ewinkuo1-sudo/diy-lm3886-amplifier/docs/03-整機配件需求.md

# BOM 與整機配件

> 採購資訊的單一入口是 [00 採購總表](00-採購總表.md)；本頁為其附錄，保留設計需求與原始判斷依據。

最新[露天商品直達連結](11-露天購物連結.md)已另列2026-09-18查價、包裝與待確認條件；以下保留設計需求。

> V0.3／2026-09-16：採用 C 方案，只有變壓器與 LM3886T 已購；額定電流、保護與實際功率待確認。

[電路 BOM](../electrical/bom-draft.csv) 由 KiCad 匯出的 netlist 產生，涵蓋 43 個放大板元件；另有[電源次級 BOM](../electrical/psu-bom-draft.csv) 的 15 個元件。`footprint` 留空代表尚未核對實際尺寸，不能據此直接下單 PCB。沒有價格欄：本次未查供應商即時庫存與報價。

## 放大板選材

- IC：LM3886T ×2 為設計用量；已訂拆機品，訂單數量與 /NOPB 待核對；封裝與引腳彎折須依實際訂購型號核對。
- 小訊號電阻：1% 金屬膜，除 BOM 另列者外以 0.25W 起選。
- Zobel 與輸出阻尼電阻：低電感、至少 2W，保留散熱空間，量測高頻下溫升。
- 0.7µH 電感：空心，初選 DCR ≤0.05Ω，線徑與安裝須能承受至少 4A 峰值及測試溫升；40W／8Ω 的需求為 3.16A 峰值。此項仍需料號或繞製規格。
- 2.2µF 輸入電容：薄膜、≥63V。
- 47µF 回授電容：真正無極性／雙極性、≥63V；不把一般電解正反接的問題留到焊接時猜測。
- 電源／靜音電解：≥63V，依原理圖正負極組裝。100nF 去耦可用 X7R 或薄膜；Zobel 用薄膜。

## 尚未畫入放大板的整機需求

| 部件 | 數量 | 初選條件／待辦 |
|---|---:|---|
| 內建環形變壓器 | 1 | 已訂 AC110V、兩組獨立 22Vac＋單 12Vac；賣場 200W 不作已確認 VA，電流／頻率／調整率待核對 |
| 整流與大電容 | 1 組 | 電源次級 BOM 已列兩橋、4×10,000µF／63V、洩放及旁路；料號與散熱待選 |
| AC 入口／一次側保險絲／開關 | 1 組 | 核對一次側料件後決定電流額定與分斷能力 |
| 浪湧控制與旁路 | 1 組 | 含快速關開及失效情境，待設計 |
| 隔離輔助電源／輔助繞組 | 1 組 | 供保護繼電器與啟停控制，待決定電壓及容量 |
| 電源動態能力／儲能 | 1 組 | 2×40W 試算同相正弦時，每軌訊號峰值約 6.32A，另有靜態電流；由實際電源與電容共同承擔，待選型後驗證 |
| 散熱器 | 2 | 每聲道 ≤0.4°C/W，按實際機內氣流及安裝方向核對 |
| 絕緣導熱介面及螺絲套 | 2 組 | 確認熱阻 ≤0.3°C/W 與電氣絕緣；不只核對厚度 |
| 絕緣 RCA 插座 | 2 | 機殼接地規劃完成前不靠插座形成多點地 |
| 喇叭接線柱 | 4 | 額定電流、絕緣距離與面板固定待選；原型先接假負載 |
| 機殼／固定件 | 1 組 | 依散熱器、電源界面及 PCB 實際尺寸設計；尚無加工圖 |
| 電源輸入保護 | 1 組 | 下一版加入適合雙軌電源的保護；不得直接套用未定案的保險絲額定 |
| 喇叭 DC 保護／繼電器 | 1 組 | 下一版設計，包含輔助電源及 DC 斷開能力驗證 |
| 非感性假負載 | 2 | 8Ω、連續至少 100W，按額定安裝散熱 |

內建電源的架構與次級整流草案已完成；一次側接線、軟啟動及保護控制尚未完成。整機 BOM 尚須加入機殼 PE 接點、屏障、端子與線束。參見[內建電源規劃](05-內建電源與機構.md)。
