ewinkuo1-sudo/diy-lm3886-amplifier/docs/09-採購後修訂計畫.md

# 採購後修訂計畫（2026-09-16）

> 採購資訊的單一入口是 [00 採購總表](00-採購總表.md)；本頁為其附錄，保留設計需求與原始判斷依據。

**2026-09-18 選料更新：**已登記使用者預計下單清單；47µF／470µF 各保留兩款候選，尚未決定。全部未購，詳見 [目前候選與封裝影響](10-預計下單清單.md)。既有 PCB／3D 外框尚未依此換料。

本文件取代 V0.2 的變壓器採購候選與功率驗收目標。使用者確認兩個商品均已下單、正在等到貨；沒有到貨量測。

## 使用者選定 C 方案：完整雙聲道

- 兩聲道各一顆 LM3886T，共用正負主電源；雙橋指正、負電源整流架構，不代表左右聲道各有獨立電源。
- 主整流橋 2 顆、10,000µF／63V 主濾波電容 4 顆（每軌 2 顆並聯）全部待購；容量配置已選，實際品牌／系列、紋波額定及尺寸待選。
- 整機納入散熱與絕緣、雙聲道喇叭 DC 保護、開機延遲／掉電斷開、浪湧限制、保險絲、機殼 PE 接地及端子配線。這些均未購且尚未完成細部設計。
- 優先評估 12Vac 輔助繞組供保護與控制，模組供電類型及繞組電流確認後選型。
- 四顆主電容不代表輸出瓦數增加；功率仍受變壓器、供電下陷與散熱限制。單聲道先測只是驗證順序，最終交付目標是完整雙聲道。

## 已下單與設計方向

- [蝦皮環形變壓器](https://shopee.tw/product/1151719/361359378)：賣場標示 200W、輸入 AC110V、輸出 (0–22)/(0–22)＋(0–12)，兩組主次級可串聯；直徑 120mm、高 43mm、約 2.4kg。這些是 2026-09-16 查閱的商品宣稱，不是驗收數據。連續 VA、各繞組電流、頻率額定、調整率、熱保護及線色相位待確認；不得直接把 200W 當 200VA 或推定每繞組電流。
- [露天 LM3886T](https://www.ruten.com.tw/item/22405749782156/)：標題為二手原裝拆機，物品狀況欄卻寫全新，來源與健康狀態待核對。已確認此連結下單，訂單數量待確認；設計需 2 顆，舊紀錄 4 顆不作已確認數量。不能把賣場 T 型號直接登記為已確認 /NOPB。
- 維持兩聲道各一顆 LM3886T、非橋接非並聯、8Ω、Z10 RCA 控制音量；放大板元件值暫不更動。
- 取消另購原 300VA／2×25Vac 候選。先沿用兩組獨立次級各接全橋、橋輸出串聯形成正負軌的架構；此接法下 AC 次級不得另行串接。到貨需先核對繞組獨立性與標記。
- 依 C 方案選定每軌 20,000µF、63V 主電容配置，實際料號待選；保留原散熱初選，不因電壓降低而逕行縮小散熱器。保險絲、浪湧限制與整流橋需依實際額定再選。

## 電壓與功率：估算而非額定

雙橋每軌有兩顆導通二極體。若次級確實為 22Vrms、每顆壓降取 1.1V，濾波峰值約 22×√2−2.2 = 28.9V，尚未扣紋波與負載下陷。因此「約 ±30V 等級」不代表固定供電。

沿用舊版的 +10% 市電、+8% 空載調整率、每顆二極體 0.6V 假設，得到 22×1.10×1.08×√2−1.2 ≈ 35.8V／軌。調整率未知，這只是情境計算，不能作最大電壓保證。

先以每聲道約 30～40W／8Ω 為探索範圍；不再要求必達 2×40W，也不沿用 50W 延伸驗收。先量削波點與溫升，再決定可標示的雙聲道連續功率。TI 的 ±28V、8Ω、典型 38W 是元件參考條件，並非本機保證。[TI LM3886](https://www.ti.com/product/LM3886)

## 12Vac 輔助繞組

優先供喇叭保護與啟停控制，但待確認繞組電流及模組 AC／DC 輸入要求。12Vac 經全橋濾波約為 15～16Vdc，空載可能更高；若模組要求 DC12V，需適當穩壓。暫緩另購輔助變壓器與未定型保護板。

## 到貨與下一步

1. 核對變壓器標籤、繞組線色／相位、額定電流、尺寸及配件；取得賣家資料後更新電源模型。機殼與保險絲待此步再選。
2. 核對 IC 實收數量、完整打標及批號；外觀不能證明真偽。T 背板為負電源，保留絕緣導熱介面與螺絲絕緣套。
3. 每顆先裝散熱器，用限流雙電源檢查靜態電流、輸出直流、波形與溫升；先單聲道、假負載測試。
4. 電源獨立量測空載、負載、紋波及放電，再整合雙聲道；DC 保護與啟停驗證後才接喇叭。
5. 放大板小零件可沿用候選清單；PCB、機殼、保護板與一次側元件仍未定案。

## 圖面與 PDF 版本

V0.3 已更新兩份 KiCad 圖的供電與版本標示、PDF／PNG 預覽、BOM 及 22Vac 電源／熱估算。原放大電路與雙橋四電容網路保留；12Vac 控制與一次側只列功能框架，待詳細設計。驗證結果見 electrical/validation.md，沒有硬體量測。

新版 PDF 位於 output/pdf/，包含現行設計彙整及採購勾選清單。2026-09-11 舊 PDF 僅作歷史快照，不作現行採購依據。六張導讀圖已於 2026-09-17 同步方案 C V0.3，見 [導讀圖索引](diagrams/README.md)；舊圖由 Git 歷史保留。
