ewinkuo1-sudo/diy-lm3886-amplifier/docs/10-預計下單清單.md

# 預計下單零件與替代候選（2026-09-18）

> 採購資訊的單一入口是 [00 採購總表](00-採購總表.md)；本頁為其附錄，保留設計需求與原始判斷依據。

使用者提供文字清單與購物車截圖，並確認 **47µF 與 470µF 的兩組品牌都先保留候選，尚未決定**。以下全部是預計下單／候選，不是已購、已出貨或到料紀錄；沒有代為購買。

[露天購買連結、下標選項及其餘待買候選](11-露天購物連結.md)已補齊；NCC店未滿$100不出貨等限制見該頁。

## 文字清單：佑昇音響／真合貿易有限公司

規格、金額及出貨天數原依使用者貼文記錄；2026-09-18已補上商品直達連結並核對商品頁，未結帳。價格暫按每顆新台幣計算；14／21 天為賣場出貨描述，不是到貨承諾。

| 品牌／系列／料號 | 規格 | 數量 | 對應原理圖 | 顯示價格／顆 | 出貨描述 | 狀態 |
|---|---|---:|---|---:|---|---|
| [Vishay BCcomponents PR02](https://www.ruten.com.tw/item/21452091096054/) | 2.2kΩ / 2W / 1% | 2 | R201, R202 | $20 | 21天內 | 預計下單，未購 |
| [RNU2（製造商待確認）](https://www.ruten.com.tw/item/21308069698811/) | 2.7Ω / 2W | 2 | R5, R105 | $5 | 21天內 | 預計下單，未購 |
| [Vishay BCcomponents PR02](https://www.ruten.com.tw/item/21452091095918/) | 10Ω / 2W / 1% | 2 | R7, R107 | $20 | 21天內 | 預計下單，未購 |
| [Vishay BCcomponents MRS25](https://www.ruten.com.tw/item/21505371267166/) | 1kΩ / 0.6W / 1% | 4 | R3, R103, R6, R106 | $5 | 14天內 | 預計下單，未購 |
| [Vishay BCcomponents MRS25](https://www.ruten.com.tw/item/21505371700382/) | 20kΩ / 0.6W / 1% | 2 | R4, R104 | $5 | 21天內 | 預計下單，未購 |
| [Vishay BCcomponents MRS25](https://www.ruten.com.tw/item/21505371269809/) | 22kΩ / 0.6W / 1% | 4 | R2, R102, R8, R108 | $5 | 21天內 | 預計下單，未購 |
| [Vishay BCcomponents MRS25](https://www.ruten.com.tw/item/21505371254476/) | 1MΩ / 0.6W / 1% | 2 | R1, R101 | $5 | 21天內 | 預計下單，未購 |
| [CDE 361R / 361R101M100EG2](https://www.ruten.com.tw/item/22111174641617/) | 100µF / 100V | 2 | C8, C108 | $48 | 21天內 | 預計下單，未購 |
| [ROE EKE](https://www.ruten.com.tw/item/21513740997288/) | 470µF / 63V | 4 | C6, C7, C106, C107 | $90 | 21天內 | 候選，二擇一 |
| [ROE EGW](https://www.ruten.com.tw/item/21515914332545/) | 47µF / 63V / 23Vac / BP-NP | 2 | C2, C102 | $300 | 21天內 | 候選，二擇一 |
| [WIMA MKS4](https://www.ruten.com.tw/item/21304180923597/) | 2.2µF / 100V / 5% | 2 | C1, C101 | $70 | 14天內 | 預計下單，未購 |
| [WIMA MKS2 / MKS2D031001A00JSSD](https://www.ruten.com.tw/item/21304114150484/) | 100nF / 100V / 5mm | 8 | C3, C4, C5, C103, C104, C105, C205, C206 | $19 | 14天內 | 預計下單，未購 |
| [CDE 381LX / 381LX103M063A052](https://www.ruten.com.tw/item/22102647676193/) | 10000µF / 63V | 4 | C201, C202, C203, C204 | $185 | 14天內 | 預計下單，未購 |
## 截圖中的替代候選

| 用途 | 文字清單 | 截圖候選 | 實際需求 |
|---|---|---|---|
| C2／C102 回授無極性電容 | ROE EGW 47µF／63V，$300×2 | [Mundorf E-Cap RAW 47µF／100V](https://www.ruten.com.tw/item/21724493448626/)，$190×2；管迷；標示3天內出貨 | 合計只需2顆，兩款尚未決定 |
| C6／C7／C106／C107 本地儲能 | ROE EKE 470µF／63V，$90×4 | [NCC KY 470µF／63V](https://www.ruten.com.tw/item/22339798786419/)，$15×4；f88911；標示3天內出貨、16×20 mm | 合計只需4顆，兩款尚未決定 |

截圖運費：管迷郵寄 $50、f88911 黑貓 $30，均為畫面當時顯示，未確認結帳。Mundorf 商品標題的「47µf」按 47µF 登記。截圖不是訂單證明。

## 數量與金額核對

文字清單共有13列、40顆，對應40個不同的原理圖位置；加入替代候選後仍為40個需求位置，不是46顆必買。所有電阻數量相符；100nF ×8 正好涵蓋兩聲道去耦4顆、Zobel 2顆、電源板旁路2顆。

若貼文價格均為單價，以下為**零件小計，不含運費與折扣**：

| 47µF 選擇 | 470µF 選擇 | 試算小計 |
|---|---|---:|
| ROE EGW | ROE EKE | $2238 |
| ROE EGW | 日本化工 NCC KY（賣場標示） | $1938 |
| Mundorf E-Cap RAW | ROE EKE | $2018 |
| Mundorf E-Cap RAW | 日本化工 NCC KY（賣場標示） | $1718 |

## 對目前 PCB／3D 的影響

這次更新選料紀錄，**未把商品名稱直接視為已驗證封裝，也未重畫 PCB**。既有 A＋B＋C 圖集是選料前的 V0.3 快照；圖中的高度及外框仍為假設。

- **C2／C102：必須重新安排臥式封裝。** ROE 文字清單與 Mundorf 截圖均為臥式候選，不能直接沿用目前立式 `BP_D10_P5` 的孔位／外框。需先確認本體長度、直徑、引腳彎折與安裝腳距。
- **470µF：NCC 候選的賣場尺寸與現板不同。** 截圖標示16×20 mm，現有占位為 Ø12.5 mm／腳距5 mm；若採 NCC，需核對完整料號與腳距並調整外框、間距及模型。ROE EKE 也未取得實體尺寸。
- **100µF：CDE 已提供完整料號。** 100V 為較高標示耐壓，仍需核對容量容差、尺寸、漏電等條件，不表示能直接塞進原 Ø8 占位。
- **主電容：CDE 381LX 已提供完整料號，但為牛角型。** 不只查腳距，也要確認接腳形狀、鑽孔及本體尺寸；現有1.3 mm孔不視為已合格。
- **電阻：軸向腳距需按本體與彎腳確認。** PR02、MRS25 的完整訂購碼尚未提供；RNU2 的4.5×15 mm只記為賣場描述，低電感特性仍待資料核對。
- **WIMA：15 mm／5 mm 腳距與目前占位方向一致，但本體寬高與完整型號仍需逐項核對。** MKS2 的完整料號已記錄；MKS4 尚缺完整訂購碼。

下一次修改封裝時，以本表候選＋原廠尺寸圖／實物為依據；再同步原板、3D、裝配圖與 DRC。這次沒有新增 ERC／DRC 或硬體測試。

## 尚未包含的零件

整流橋、次級保險絲及座、0.7µH電感、板端接頭／跳線、RCA與喇叭端子、散熱器與絕緣件、機殼固定件、保護／啟停／輔助電源及一次側配件仍需確認。變壓器與LM3886T沿用既有已訂待到貨紀錄。

## 資料來源與狀態

本表來源僅為使用者2026-09-18提供的文字與截圖，不把商品標題當成原廠認證。完整結構化紀錄見 [JSON](10-planned-parts.json)；已購狀態見 [採購紀錄](08-採購狀態.md)。未把含商店與價格的原始截圖上傳到專案。
