ewinkuo1-sudo/diy-lm3886-amplifier/docs/11-露天購物連結.md

# 露天商品連結與待買候選（2026-09-18）

> 採購資訊的單一入口是 [00 採購總表](00-採購總表.md)；本頁為其附錄，保留設計需求與原始判斷依據。

這份清單可直接點到商品頁，再由使用者選規格、數量與加入購物車。**沒有新增訂單或代加購物車；47µF、470µF仍各自二擇一、尚未決定。** 全部商品頁已於2026-09-18開啟核對，看到購物操作入口；價格、庫存、可選規格與出貨條件以結帳當時為準。

「原清單相符」只代表賣場描述符合使用者選的候選，並非原廠資料、真偽、實測或PCB封裝核對。「待確認／暫緩」的新增候選，應先解決該列缺項才購買。這不是一鍵全買清單。

## 原本15項候選的商品直達連結

前13項為佑昇音響／真合貿易有限公司（yosontw），最後兩項為截圖指定賣家。數量為雙聲道設計需求，價格為單顆；完整位置對照與原始採購紀錄見[原清單](10-預計下單清單.md)。

| 商品直達頁 | 規格 | 設計需求 | 單顆參考價 | 選項／注意 |
|---|---|---:|---:|---|
| [Vishay BCcomponents PR02](https://www.ruten.com.tw/item/21452091096054/) | 2.2kΩ / 2W / 1% | 2 | $20 | 單件商品；需求2顆 |
| [RNU2（製造商待確認）](https://www.ruten.com.tw/item/21308069698811/) | 2.7Ω / 2W | 2 | $5 | 單件商品；需求2顆 |
| [Vishay BCcomponents PR02](https://www.ruten.com.tw/item/21452091095918/) | 10Ω / 2W / 1% | 2 | $20 | 單件商品；需求2顆 |
| [Vishay BCcomponents MRS25](https://www.ruten.com.tw/item/21505371267166/) | 1kΩ / 0.6W / 1% | 4 | $5 | 單件商品；需求4顆 |
| [Vishay BCcomponents MRS25](https://www.ruten.com.tw/item/21505371700382/) | 20kΩ / 0.6W / 1% | 2 | $5 | 單件商品；需求2顆 |
| [Vishay BCcomponents MRS25](https://www.ruten.com.tw/item/21505371269809/) | 22kΩ / 0.6W / 1% | 4 | $5 | 單件商品；需求4顆 |
| [Vishay BCcomponents MRS25](https://www.ruten.com.tw/item/21505371254476/) | 1MΩ / 0.6W / 1% | 2 | $5 | 單件商品；需求2顆 |
| [CDE 361R](https://www.ruten.com.tw/item/22111174641617/) | 100µF / 100V | 2 | $48 | 選「1個」，數量2 |
| [ROE EKE](https://www.ruten.com.tw/item/21513740997288/) | 470µF / 63V | 4 | $90 | 單件商品；需求4顆；與同組另一款二擇一 |
| [ROE EGW](https://www.ruten.com.tw/item/21515914332545/) | 47µF / 63V / 23Vac / BP-NP | 2 | $300 | 單件商品；需求2顆；與同組另一款二擇一 |
| [WIMA MKS4](https://www.ruten.com.tw/item/21304180923597/) | 2.2µF / 100V / 5% | 2 | $70 | 選「1顆」，數量2；不要選10顆包裝 |
| [WIMA MKS2](https://www.ruten.com.tw/item/21304114150484/) | 100nF / 100V / 5mm | 8 | $19 | 選「1個」，數量8 |
| [CDE 381LX](https://www.ruten.com.tw/item/22102647676193/) | 10000µF / 63V | 4 | $185 | 選「1個」，數量4；不要選10個包裝 |
| [Mundorf E-Cap RAW](https://www.ruten.com.tw/item/21724493448626/) | 47µF / 100V / 無極性 | 2 | $190 | 單件商品；需求2顆；與同組另一款二擇一 |
| [日本化工 NCC KY（賣場標示）](https://www.ruten.com.tw/item/22339798786419/) | 470µF / 63V | 4 | $15 | 單件商品；需求4顆；與同組另一款二擇一 |

- **NCC賣場最低出貨金額：**[f88911公告](https://www.ruten.com.tw/store/f88911/)表示未含運低於$100不出貨；4顆×$15＝$60尚未達門檻。購買前確認合單或出貨條件，勿把多買的備品當成電路需求。
- WIMA MKS4頁面含1顆／10顆選項；CDE 381LX含1個／10個。表內以單件需求計，不能按最低顯示價誤選整包數量。
- Mundorf賣方新增尺寸描述為本體Ø14×37mm、引線長60mm，仍需原廠／到料核對；不把引線長當PCB腳距。NCC原款是16×20mm，不是同店的12.5×30mm款。
- 原13項小計仍為$2238；依兩組替代選擇為$1938／$2018／$1718，皆未含運、最低出貨門檻及新增配件。

## 尚未選購的板上元件與整機配件

以下都是新找到的候選來源，**沒有替使用者定案**。需求涵蓋現有三板及整機配件；額外保護模組尚未整合原理圖。包裝單位不明的條目已標出，不能把「設計需求」直接當下標件數。

### 電源板

| 商品直達頁 | 設計需求 | 選項／頁面價格 | 選型狀態與待核對 |
|---|---|---|---|
| [KBPC2510 整流橋](https://www.ruten.com.tw/item/22605098060064/) | 2個／BR1、BR2 | 標題25A／1000V，單位數量先確認；$51 | 待確認：完整廠牌、KBPC／KBPC-W端子形態、腳位、外形與散熱；25A不能當作本板持續輸出能力。 |
| [5×20mm 保險絲座](https://www.ruten.com.tw/item/21840721329469/) | 2個／F201、F202 | 保險絲座，不把附帶保險絲當已選定；$4 | 待確認：PCB安裝型態、腳距、孔徑、DC電壓／電流額定；5×20是保險管尺寸，不是焊腳距。 |

### 放大板

| 商品直達頁 | 設計需求 | 選項／頁面價格 | 選型狀態與待核對 |
|---|---|---|---|
| [0.7µH 空心電感](https://www.ruten.com.tw/item/22615433056210/) | 2個／L1、L2 | 每件1只，需求2；$379 | 待確認：賣方稱線徑2.1mm、外徑13.5mm、長10.5mm、腳距28mm；DCR≤0.05Ω、≥4A峰值與公差未證實，2.1mm線徑須重新核對PCB孔徑。 |

### 接插件

| 商品直達頁 | 設計需求 | 選項／頁面價格 | 選型狀態與待核對 |
|---|---|---|---|
| [KF301 2P／5.08mm](https://www.ruten.com.tw/item/22409916143944/) | 6個 | 2P，賣方標300V／16A、14–22AWG；確認1件所含數量；$1 | 待確認：J1／J2各2個＋J201／J202各1個；廠牌、孔徑、插線方向與載流條件，不能只憑同為KF301認定相容。 |
| [KF301 3P／5.08mm](https://www.ruten.com.tw/item/22410924930141/) | 3個 | 3P，賣方標300V／16A、14–22AWG；確認1件所含數量；$2 | 待確認：左右板J5各1個＋J203一個；核對VCC/GND/VEE順序、孔徑、插線方向與載流。 |
| [2.54mm 單排針 1×40P](https://www.ruten.com.tw/item/21839712907740/) | 2段×2pin | 一條40pin可裁出兩段；先確認單件包裝；$3 | 待確認：RUN JP1／JP2，與跳線帽配合高度、≥60VDC絕緣額定；不是排母。 |
| [2.54mm 跳線帽](https://www.ruten.com.tw/item/22410924645672/) | 2個 | 商品為100只包裝；買1包會剩98只；$23／100只 | 待確認：≥60VDC絕緣額定；僅採購包裝超額，不增加設計需求。 |

### 機殼接插件

| 商品直達頁 | 設計需求 | 選項／頁面價格 | 選型狀態與待核對 |
|---|---|---|---|
| [RCA 面板母座](https://www.ruten.com.tw/item/21840724685995/) | 2個 | 紅色1、黑色1；$12 | 待確認：必須附能隔離外殼與金屬面板的完整絕緣墊圈／套管；目前只確認紅黑款商品頁，沒有證明面板絕緣。 |
| [喇叭接線柱](https://www.ruten.com.tw/item/22410923188279/) | 4個 | 標題1只價；需求紅2、黑2，頁面未提供顏色選項，需先確認配色方式；$17 | 待確認：≥60VDC、載流、面板絕緣、開孔及板厚；不是4個單聲道端子組。 |

### 散熱／機構

| 商品直達頁 | 設計需求 | 選項／頁面價格 | 選型狀態與待核對 |
|---|---|---|---|
| [大 TO-3P 雲母絕緣片 22×30mm](https://www.ruten.com.tw/item/22410921549515/) | 2片 | 10張包裝，1包；$23／10張 | 待確認：此為尺寸候選，尚未證明適合LM3886T孔位／金屬背板；整套介面熱阻≤0.3°C/W、耐壓及安裝公差待核對。 |
| [LM3886 用絕緣螺絲套](https://www.ruten.com.tw/item/21711492321878/) | 2個 | 10顆包裝，1包；$20／10顆 | 待確認：賣方列外徑6mm／內徑3mm；套肩長、IC孔位與實際螺絲配合；螺絲套不取代導熱絕緣片。 |
| [TS-KS101 導熱膏](https://www.ruten.com.tw/item/22410921235113/) | 裝配適量 | 45g包裝，需求1份；$57 | 待確認：材料導電性與介面相容；導熱膏不能單獨提供LM3886T背板絕緣。 |
| [大型鋁型材散熱器](https://www.ruten.com.tw/item/22407792090091/) | 每聲道1個，條件成立才採買 | 頁面有「200長（批量）」與「100長（批量）」；尺寸與最小包裝需詢明；$1,012–2,531 | 暫緩：標題400×50×200mm，沒有≤0.4°C/W資料，並可能超出機殼空間；僅作詢問熱阻／裁切的來源，未認定合用。若用附散熱器機殼不要重複買。 |
| [430寬全鋁後級機箱](https://www.ruten.com.tw/item/22547543033963/) | 1個 | 有300深度／400深度；以400深度作排布候選，未定案；$3,895–4,285 | 暫緩：賣方400深款內部約330×112×400mm，附兩側散熱器及帶保險電源座；尺寸標題／內文有差異，須取加工圖。散熱片重量不是熱阻，三板／變壓器／保護板仍需排布。 |
| [M3 銅柱、螺絲、螺帽](https://www.ruten.com.tw/item/22601863290504/) | 三片PCB共12支柱，螺絲依安裝方式 | 先選M3，長度待機構定案；銅柱10個/包，若買兩包則20支；螺絲為另一選項；$25–95 | 待確認：板底焊腳間隙、銅柱高度、螺絲長度與接地用途；勿將M4或單買螺母選項當成完整固定組。 |

### 市電／控制

| 商品直達頁 | 設計需求 | 選項／頁面價格 | 選型狀態與待核對 |
|---|---|---|---|
| [AC-01 電源入口＋帶燈開關＋保險座](https://www.ruten.com.tw/item/22410919510431/) | 1組（機殼若已附合用款則免重買） | 賣方標15A／250V，需確認110Vac燈與接口規格；$29 | 暫緩：核對原廠安規、極數、接地端、一次側開關接法、面板尺寸與保險管；保險絲電流尚未決定。 |
| [5×20 延時保險絲系列](https://www.ruten.com.tw/item/22410976060232/) | 至少一次側1＋次級2，最終依保護設計 | 標題1／1.5／2／3／3.15A；沒有可直接指定的正確電流，包裝數量也待確認；$136（單位未明） | 暫緩：變壓器額定電流、浪湧、保護協調、AC/DC分斷能力未定；不保證此系列任一款符合，禁止照頁面預設值購買。 |
| [AC105–235V 軟啟動板](https://www.ruten.com.tw/item/22546454641812/) | 1組 | 接線端子式／插線端子式兩款；接線端子式先列候選；$660 | 暫緩：僅標題電壓範圍涵蓋110V；需電路／額定功率、限流電阻、繼電器、重啟及失效行為，尚未整合設計。 |
| [UPC1237 雙聲道喇叭保護板](https://www.ruten.com.tw/item/22631277223445/) | 1組 | 賣方稱獨立AC12–18V、約3秒延遲、約1VDC起控；$258 | 暫緩：賣家公告部分二手以全新欄位上架，需確認本件狀況。需完整電路、±DC偵測、掉電釋放、繼電器DC分斷能力及12Vac繞組容量；不可將300Wx2文案當規格。 |

### 線束

| 商品直達頁 | 設計需求 | 選項／頁面價格 | 選型狀態與待核對 |
|---|---|---|---|
| [16AWG 黑色矽膠線](https://www.ruten.com.tw/item/22407795970619/) | 長度待機殼排布 | 1米單位；先列候選，不先固定米數；$35／米 | 待確認：銅截面、溫度／電壓額定、端子適配；供次級／DC／喇叭線路評估，不自動作市電或PE線。 |
| [16AWG 紅色矽膠線](https://www.ruten.com.tw/item/22407795970226/) | 長度待機殼排布 | 1米單位；不同電源軌需另做清楚標識；$35／米 | 待確認：同黑色線要求，實際束線載流與溫升仍需驗證。 |
| [20cm 屏蔽訊號線](https://www.ruten.com.tw/item/22325050050240/) | 左右聲道各1段，長度待確認 | 原商品帶XH2.54 3P插頭；$8 | 待確認：現板J1是2P／5.08，不可直接插接，僅線材候選；需改端接、確認屏蔽芯線及實際長度。 |

### 測試

| 商品直達頁 | 設計需求 | 選項／頁面價格 | 選型狀態與待核對 |
|---|---|---|---|
| [8Ω／100W 鋁殼電阻](https://www.ruten.com.tw/item/21840720484921/) | 2個 | 標稱8Ω／100W；散熱器另需核算；$40 | 未符合完整需求：賣方未證實非感性及100W額定散熱條件；本頁僅阻值／功率候選，不列為已核准假負載，不可據此做高頻驗收。 |

## 尚未補到可採用商品的缺項

不是所有缺項都有足夠資料完成選型；以下保留明確缺口，不以規格不符的商品充數。

| 缺項 | 目前限制 |
|---|---|
| 台灣三腳插頭至IEC C13電源線 | 本次尚未取得可核對BSMI與正確接頭的商品直達頁；不要用兩芯線或梅花尾替代。 |
| PE黃綠接地線、環形端子、星形華司與獨立機殼接地螺栓 | 本次未核實適合的完整組合；線徑、端子孔徑、壓接及固定須隨一次側／機構定案。防靜電手環線不能作PE。 |
| 絕緣屏障、套管、護線圈、束線固定與機腳 | 依機殼孔位、線徑及材料等級選定，尚無確定尺寸，未隨意填商品。 |
| 獨立狀態指示燈／輔助穩壓 | 保護板帶LED、AC入口帶燈；先確認是否仍需要獨立前面板燈。12Vac繞組優先，不另訂變壓器或固定DC模組。 |

## 對目前PCB的影響

商品連結不會使PCB自動適配。尤其臥式47µF、Ø16mm NCC、本次0.7µH電感的粗引腳、KBPC端子以及保險絲座都要先取得尺寸，再修改封裝與檢查。此次未修改原理圖、PCB、3D、Gerber或既有PDF，也沒有新增ERC／DRC或硬體測試。

本頁38個商品直達連結包含原候選15項＋新增23項。機器可讀資料：原候選在[10-planned-parts.json](10-planned-parts.json)，新增候選／未解決項目在[11-ruten-shopping-links.json](11-ruten-shopping-links.json)。後續確認選料時，先更新候選狀態，再改PCB，不從本頁反推已購或已驗證。
