ewinkuo1-sudo/diy-lm3886-amplifier/docs/12-機殼候選.md

# 12 機殼候選（淘寶，2026-09-18 查）

> 採購資訊的單一入口是 [00 採購總表](00-採購總表.md)；本頁為其附錄，保留設計需求與原始判斷依據。

**本文件是選型調查，不是採購決定。所有尺寸為賣場標題標示的外部尺寸，未向賣家確認內部可用空間，未核對散熱熱阻，未下單。** 台幣為淘寶頁面自帶換算，**不含運費與集運**。

## 1. 需求推導

依 V0.3 C 方案現有文件：

| 項目 | 尺寸／需求 | 來源 |
|---|---|---|
| 環形變壓器 | Ø120 × H43 mm、約 2.4kg | [09 採購後修訂計畫](09-採購後修訂計畫.md)，賣場宣稱 |
| 電源板 | 160 × 120 mm | [README](../README.md) PCB V0.3 |
| 放大板 | 100 × 90 mm × 2 片 | 同上 |
| 主濾波電容 | 10,000µF／63V × 4，**料號未選** | [08 採購狀態](08-採購狀態.md) |
| 散熱 | 每聲道 ≤0.4 °C/W、介面 ≤0.3 °C/W，每聲道耗散約 20–23W | [05 內建電源與機構規劃](05-內建電源與機構.md)、[02 功率與散熱估算](02-功率與散熱估算.md) |
| 絕緣 | **LM3886T 背板為 VEE**，鎖上接地機殼必須用絕緣介面與螺絲絕緣套 | [01 設計規格](01-設計規格.md) |

推得最低內部空間：

- **寬 ≥ 300 mm** — 環牛（含固定盤約 140）＋電源板 160 並排
- **深 ≥ 250 mm** — 環牛 120 ＋電源板 120／160 前後排列，另需線束空間
- **高 ≥ 90 mm** — 被主電容卡住：Ø35 × 50 mm snap-in 加腳座約需 70 mm；若選牛角式（如 CDE 381LX）需 110 mm 以上

**高度需求會隨主電容選型改變。電容料號未定前，機殼高度不應定案。**

另需容納：市電入口／開關／保險絲、浪湧限制、喇叭 DC 保護板、PE 機殼接地點。

## 2. 首選

### ¥408（約 NT$1,960）4312A 兩側散熱全鋁功放機箱 430 × 120 × 311 mm

<https://www.taobao.com/list/item/V0lLOFBGSFJKTXZKS0Nrc0txaW9FQT09.htm>

唯一三圍全部標示、且兩側帶散熱的候選。430 寬容得下環牛與電源板並排，311 深可容環牛（120）＋電源板（160）前後排列，120 高即使改用牛角電容也有餘裕。評分 5.0。

## 3. 次選

### ¥315（約 NT$1,513）全銀色兩側散熱全鋁機箱 360 × 120 × 275 mm

<https://www.taobao.com/list/item/aG5UZU02OTVHVmZRTGx4TTF5anJRZz09.htm>

比首選便宜約 NT$450，仍在需求之上。深 275 放環牛加電源板較擠，走線與一次側元件空間變少。評分 5.0。

### ¥338（約 NT$1,623）3212 兩側散熱小甲機箱

<https://www.taobao.com/list/item/V3J3K3Fud2RZK1Z3TWJkTzQrMDF2dz09.htm>

型號推測為 320 寬 × 120 高，**深度未標示，需向賣家確認**。評分 5.0。

## 4. 替代路線：素機箱 ＋ 另購散熱鋁擠

總價可壓到約 ¥270（NT$1,300）以下，但**需自行加工開孔、對位，並處理散熱片與機箱的機械與熱介面**。

素機箱：

- ¥198（NT$951）3690 全鋁 360 × 90 — <https://www.taobao.com/list/item/dXJmQnllY3NvNVpSY2h6QU1iblZjdz09.htm>
- ¥178（NT$855）3290 全鋁 320 × 92 — <https://www.taobao.com/list/item/T3N6WjAvQjNBbGcvT0RkR3ZNMDFydz09.htm>

散熱鋁擠：

- ¥59（NT$283）寬 300 × 高 85 mm — <https://www.taobao.com/list/item/WEZZV29JZnRSWTVQRGxQNmlvRHNxZz09.htm>
- ¥75（NT$360）寬 350 × 高 80 mm 高倍齒 — <https://www.taobao.com/list/item/M1RITFJBWWQ2WlBMVHJhZmkwVkpvZz09.htm>
- ¥105（NT$504）寬 300／400 × 高 50 mm — <https://www.taobao.com/list/item/KzlOOUJuaGEvWGVrZHRwc3RuWFBFUT09.htm>

## 5. 已排除

| 商品 | 價格 | 排除理由 |
|---|---|---|
| [1560 機箱 151 × 60，標題寫「適合安裝 LM3886/LM1875」](https://www.taobao.com/list/item/elpFWWwrLzdLejVLczFZNncvZXE3UT09.htm) | ¥85 | **標題有 LM3886 但尺寸不可能**。環牛直徑就 120 mm |
| [BRZHiFi BZ3207S 單側散熱](https://www.taobao.com/list/item/TUtXRjhBN3dENy9jU1E1VkVpZmprdz09.htm) | ¥198 | 型號推測高度僅 70 mm，主電容立不起來；且僅單側散熱 |
| [BRZHiFi 2107 兩側散熱](https://www.taobao.com/list/item/YU4yb1hKN2ZDL2RzVTdORHJwWnJJZz09.htm) | ¥155 | 型號推測 210 × 70 mm，過小 |
| [430 × 200 純後級大功率散熱機箱](https://www.taobao.com/list/item/Y2xqTU1NSStvMitVeGFiRFg2eTA1dz09.htm) | ¥780 | 高度 200 mm 對本機過剩，價格近首選兩倍 |
| LM833+LM3886 / 5532+LM3886 功放機 | ¥989–998 | **是整機成品，不是機殼**。搜尋結果混入 |

## 6. 下單前必須確認

1. **散熱熱阻**：所有候選都只標尺寸，**沒有任何一個標 °C/W**。需求是每聲道 ≤0.4 °C/W，必須自行按鰭片面積估算或到料實測
2. **內部可用空間**：標示為外部尺寸，扣除側板與散熱片基座厚度後的淨空間未知
3. **型號推測的尺寸**：3212、2107、3207 的長寬高是依命名慣例推的，**不是賣家標示**
4. **主電容選型先於機殼**：高度需求由電容決定，見 [10 預計下單清單](10-預計下單清單.md)
5. **變壓器到貨核對**：實際直徑、高度與固定件尺寸需以實物為準，賣場 Ø120 × 43 未經驗證
6. **絕緣介面**：LM3886T 背板帶 VEE，兩側散熱機箱的側板通常與機殼共構並接 PE，必須確認絕緣墊片與絕緣套方案
7. 運費與集運成本未計入

## 7. 查詢方法備註

淘寶搜尋頁（`s.taobao.com/search`）為 JS 渲染，無法直接讀取。可用的是關鍵字落地頁 `https://www.taobao.com/list/product/<關鍵字>.htm`，標題、價格、台幣換算與評分均可取得；**商品詳情頁不含規格文字**，故本文件所有尺寸皆來自商品標題。

查詢關鍵字：`全铝功放机箱`、`后级功放机箱`、`铝合金功放机箱`、`功放机箱diy`、`大功率功放机箱`、`lm3886功放机箱`、`全铝机箱`，共取得 126 筆去重商品。
