ewinkuo1-sudo/diy-lm3886-amplifier/docs/08-procurement.md

# 採購狀態

[露天商品連結與缺項表](11-ruten-shopping-links.md)（2026-09-18）：原清單15項＋新增23項商品；候選未購，保險絲／散熱／保護控制尚未定案。

**2026-09-18 選料更新：**已登記使用者預計下單清單；47µF／470µF 各保留兩款候選，尚未決定。全部未購，詳見 [目前候選與封裝影響](10-planned-parts.md)。既有 PCB／3D 外框尚未依此換料。

> 2026-09-17 使用者確認：已訂 LM3886T 與變壓器均在寄送中，尚未收到。本次 PCB B／V0.2 修訂未新增其他採購或實物核對紀錄。

更新：2026-09-16。使用者更正：真正已下單的只有下列變壓器與 LM3886T 兩個商品連結，均待到貨；電容、整流橋及其他料件全部未購。已選 C 方案：完整雙聲道、雙橋、四顆主濾波電容。

| 料件 | 狀態與規格 | 數量紀錄 |
|---|---|---|
| [環形變壓器](https://shopee.tw/product/1151719/361359378) | 已下單待到貨；賣場 200W、AC110V、兩組獨立 22Vac＋單 12Vac；VA 與各繞組電流未知 | 設計用量 1 個，訂單數量未另核對 |
| [LM3886T 拆機品](https://www.ruten.com.tw/item/22405749782156/) | 已下單待到貨；賣場標題二手拆機、狀況欄全新，需核對；/NOPB 未確認 | 訂單數量待確認；雙聲道設計需 2 顆，不將舊紀錄 4 顆視為已確認數量 |

電源與功率調整見 [採購後修訂計畫](09-purchased-plan.md)。已購不等於已驗收，沒有量測結果。

## 到料核對

- 變壓器標籤、引線、繞組獨立性、相位、電流、頻率、熱保護及空載電壓。
- IC 數量、封裝、完整打標、批號及引腳狀況；外觀不能保證真偽。若收到不同封裝，先核對機構與熱阻，不直接代換。
- 裝妥散熱與電氣絕緣後，以限流電源和假負載逐顆測試直流、靜態電流、波形及溫升。

## 採購紀錄更正

舊版記載「KBPC2510 ×1、Nichicon 10,000µF／63V ×2 已下單」不正確，依使用者本次更正撤銷。不是退貨或取消訂單，而是先前紀錄錯誤。

## 其餘全部未購

散熱器、絕緣介面、輸出電感、一次側元件、浪湧控制、保護板、機殼及其他被動件均未購。原 300VA／25Vac 變壓器不再採買；額外輔助電源先暫緩，優先評估 12Vac 繞組。

CSV BOM 是由 V0.3 KiCad netlist 自動產生的設計用量，不是庫存或訂單清單；本檔獨立保存採購事實。PCB 與 footprint 尚未定案。

## C 方案待採購清單（設計用量，實際料號待核對）

### 電源板（全部未購）

| 料件 | 規格 | 還需 | 對應 | 備註 |
|---|---|---:|---|---|
| 橋式整流器 | KBPC2510 25A/1000V 可作候選，非指定料號 | 2 | BR1、BR2 | 兩組獨立次級各一橋；核對浪湧、腳位與散熱 |
| 主濾波電容 | 10,000µF／63V 電解，品牌／系列待選 | 4 | C201–C204 | 每軌 2 顆並聯，共 20,000µF／軌；核對紋波電流、壽命、尺寸與腳距 |
| 100nF/100V 薄膜電容 | 旁路 | 2 | C205、C206 | |
| 2.2kΩ/2W 電阻 | 洩放 | 2 | R201、R202 | 金屬皮膜或金屬氧化膜 |

### 放大板被動元件（全部待買）

**電阻（1% 金屬皮膜，0.25W 除非另標）**

| 值 | 數量 | 對應 | 備註 |
|---|---:|---|---|
| 1MΩ | 2 | R1、R101 | 輸入洩放 |
| 22kΩ | 4 | R2、R8、R102、R108 | 輸入偏壓＋靜音 |
| 20kΩ/1% | 2 | R4、R104 | 回授上臂，決定增益 |
| 1kΩ/1% | 2 | R3、R103 | 回授下臂，決定增益 |
| 1kΩ | 2 | R6、R106 | 輸入串聯 |
| 2.7Ω/2W | 2 | R5、R105 | Zobel，低電感 |
| 10Ω/2W | 2 | R7、R107 | 輸出隔離，低電感 |

**電容**

| 值 | 數量 | 對應 | 備註 |
|---|---:|---|---|
| 2.2µF/63V 薄膜 | 2 | C1、C101 | 輸入隔直 |
| 47µF/63V 無極性（BP） | 2 | C2、C102 | 回授，必須真正雙極性 |
| 100nF/63V | 4 | C3、C4、C103、C104 | 電源去耦（薄膜或 X7R） |
| 100nF/100V 薄膜 | 2 | C5、C105 | Zobel |
| 470µF/63V 電解 | 4 | C6、C7、C106、C107 | 本地儲能，注意極性 |
| 100µF/63V 電解 | 2 | C8、C108 | 靜音電容，正端 GND 負端 MUTE |

**電感**

| 值 | 數量 | 對應 | 備註 |
|---|---:|---|---|
| 0.7µH 空心 | 2 | L1、L2 | DCR ≤0.05Ω，≥4A，料號或繞製規格待定 |

### 接插件（規格待最終確認）

| 項目 | 數量 | 備註 |
|---|---:|---|
| 絕緣 RCA 插座 | 2 | 面板安裝，機殼接地規劃完成前不靠插座形成多點地 |
| 喇叭接線柱 | 4 | ≥60V DC 額定 |
| 電源線束插座（J5/J203） | 1 組 | 機內連接，pin 定義 VCC/GND/VEE |
| RUN 跳線座 | 2 | 靜音控制，≥60V DC 額定 |

以上沿用遠端待買明細，不表示已驗證實際元件或 footprint。
