ewinkuo1-sudo/diy-lm3886-amplifier/docs/05-internal-power.md

# V0.3 C 方案內建電源與整機規劃

兩顆 LM3886T 構成雙聲道純後級，由 Eversolo DAC-Z10 的可調 RCA 輸出控制音量。兩聲道共用正負主電源，非橋接、非並聯，也非左右獨立的雙單聲道電源。

## 主電源接法

已下單變壓器的賣場規格為 AC110V，兩組獨立 22Vac＋單 12Vac，標示 200W；VA、各繞組電流、頻率額定、調整率與熱保護待確認。兩組主次級保持彼此獨立：

1. 第一組 22Vac 接 J201，經 F201 接 BR1 AC 端。BR1 正端為 VCC，負端為 GND。
2. 第二組 22Vac 接 J202，經 F202 接 BR2 AC 端。BR2 正端為 GND，負端為 VEE。
3. BR1 負端與 BR2 正端於儲能電容匯流點形成 GND。AC 端不預先互連，不可混用單橋中心抽頭接法。
4. C201、C202 正端接 VCC、負端接 GND；C203、C204 正端接 GND、負端接 VEE。每顆 10,000µF／63V，每軌兩顆並聯成 20,000µF。
5. 每軌並聯 100nF／100V 薄膜旁路及 2.2kΩ／2W 洩放電阻。
6. J203 的 1／2／3 接放大板 J5 的 1／2／3，分別為 VCC／GND／VEE。兩份獨立原理圖需實際線束連接。

兩顆整流橋、四顆主電容全部未購。橋候選至少 15A／200V，KBPC2510 只是一個候選，不代表已選定料號；仍核對浪湧電流、冷卻與真實腳位。AC1／AC2／P／N 是原理圖功能端子，尚未指定 footprint。

## 12Vac 與控制

12Vac 優先留給雙聲道喇叭 DC 保護、繼電器及啟停控制，尚未畫成可施工的控制電路。先確認繞組電流，再依模組規格決定 AC12V 直入或整流、濾波、穩壓成 DC12V。整流後不等於 DC12V；空載電壓也需量測。

整機要求正負 DC 故障偵測、開機延遲接通、掉電快速斷開、雙軌監測與過溫控制。兩個 MUTE 節點不直接相接；測試跳線不取代整機自動控制。繼電器須核對實際 DC 斷開能力。

## 電壓與功率邊界

依 22Vac 假設估算約 ±30V 等級。高市電 +10%、空載調整率 +8% 情境得到約 ±35.8V，36V 僅用作熱情境，不是保證上限。繞組額定電流未知，不能保證 2×40W。30～40W／8Ω 為探索範圍，最終以削波、雙聲道連續負載及溫升測試定額定。[電源計算](06-mains-calculations.md)

## 一次側與機構待辦

| 項目 | 現行要求 | 待完成 |
|---|---|---|
| AC 入口、開關、保險絲 | 機內供電 | 額定、分斷能力、隔離與防觸碰 |
| 浪湧限制 | 對應四顆主電容充電 | 冷啟動、快速關開、旁路失效驗證 |
| PE 保護接地 | 機殼專用可靠固定點 | 不經開關、保險絲或音訊地阻抗元件 |
| 散熱器及介面 | 每聲道 ≤0.4°C/W、介面 ≤0.3°C/W 初選 | 核對真實料號、氣流及安裝；T 背板為負電源 |
| 機殼 | 電源、訊號、放大及控制分區 | 依實際尺寸定開孔與固定 |

變壓器中心螺栓不可與機殼形成穿過中心的封閉導電匝。電源／整流充電回路遠離輸入，避免喇叭大電流流經訊號地。[Talema 安裝提醒](https://talema.com/products/toroidal-transformers-open-style/)

本版主次級與放大板可編輯圖已更新；一次側、12Vac 控制與保護仍是功能規劃，不是完整市電施工圖。沒有 PCB、加工圖或實機驗證。[TI 電源設計參考](https://www.ti.com/lit/an/snaa057c/snaa057c.pdf)
