ewinkuo1-sudo/diy-lm3886-amplifier/electrical/preview/control-v01.pdf

1 | 2 | 3 | 4 | 5 | 6 | 7 | 8
1 | 2 | 3 | 4 | 5 | 6 | 7 | 8

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
### F Date: 2026-10-01

KiCad E.D.A. 10.0.6 | Id: 1/1
Size: A3 | Rev: 0.6 FIRST DRAFT

# Title: LM3886 V0.6 control / protection board (CTRL) - low voltage only

### File: control-v01.kicad_sch

### Sheet: /

### V0.6 control board / circuit draft only / no hardware measurements

1 | 2 C301
2200u / 25V
1 | 2 C305
47u / 16V DELAY

1

1

2

2 J309 GND TO PSU STAR (one point) 1

1

2

2 J307
FRONT LED GREEN (A, K)
1 | 2 C303
10u / 25V
1 | 2 R312
220k
1 | 2 R310
1k GREEN

A

A | C

C

E

E K

K U304
SFH617A-3 (Vceo 70 V)
1 | 2 R303
1k

1

1

2

2 J308

FRONT LED RED (A, K->RLY) | 1 | 2 R309
1k
1 | 2 R305
56k

1

1

2

2 J304
AMP L JP1 (RUN, VEE) A
A | C

C

E

E K

K U303

SFH617A-3 (Vceo 70 V) K

1

A 2 D303
1N4007 flyback
1 | 2 C308
22u / 25V
1 | 2 C306
100u / 16V (datasheet 330u) | GND GND
IN IN | OUT OUT U301
7812 (TO-220, to chassis)

K

1

A 2 D305

1N4148 (fast reset) | 1

1

2

2 J302
AMP L OUT -> SPK L+

K

1

A 2 D306
1N4007

K

1

A 2 D307
1N4007

K

1

A 2 D308
1N4007

1

1

2

2 J301
T1 12VAC
1 | 2 C302
100n

A

A K

K

REF REF U305
TL431 (2.5 V comparator)

B

B

C
C

E

E Q301 BC327-40 (PNP, 800 mA) 1 2 R304

56k

1

1

2

2 J306

TO MAINS K_BYP COIL (BYP_HI, GND) | 1

1

2

2 J303
AMP R OUT -> SPK R+

K

1

A 2 D301
1N4148

A1 A1

A2 A2 | COMCOM

NO NO K302 G2RL-1-E 12VDC

B

B

C
C

E

E Q302 BC327-40

1 | 2 R301
3.3k
1 | 2 R302
56k

K

1

A 2 D302
1N4007 flyback
1 | 2 C307
4.7u / 25V
1 | 2 R313
2.2k
1 | 2 R315
1M hysteresis
1 | 2 R311
1.5k RED

1

1

2

2 J305
AMP R JP1 (RUN, VEE)

K

1

A 2 D309
1N4007
1 | 2 R308
10k
1 | 2 R306
56k

A1 A1

A2 A2 | COMCOM

NO NO K301 G2RL-1-E 12VDC

1 | 2 R307
10k
1 | 2 R314
1k
1 | 2 C304
100n

OVL 1 DC 2

LATCH 3

ACOFF 4 | GND

5 RLY 6 DELAY 7

VREF 8 U302 UPC1237 SIP-8

RLY Q1B Q1B

AC_B | +12V
AC_A | Q1B

BYP_HI

RAW

RAW

Q2B | +12V | BYP_HI GND

GND

GND

VREF

GND

GND

RLY

DELAY

AMP_L_OUT +12V

SPK_L RLY GND

RLY

GND

LED_R

AMP_R_OUT SPK_R

LED_G

GND

LED_G

SPK_R

GND

AMP_R_OUT +12V +12V | SPK_L AMP_L_OUT RLY | RLY

LED_R

GND

AC_A

# RLY RLY

GND

OPTO_A

RAW

OPTO_M

# RUN_L VEE_L

GND

VEE_L

GND

RAW

RUN_L

GND

GND

RAW

OPTO_M

AC_B

RUN_R

GND

VEE_R

GND

VEE_R

GND

DCDET | RUN_R
AMP_R_OUT | DCDET | ACDET DCDETGND
AMP_L_OUT ACSENSE | AC_A

TLK

ACDET | ACDET ACDET | GND

TMR

TMR +12V +12V

TMR | BYP_HI TMR | GND
GND
TMR | OPTO_A

TLK

TLK | Q2B +12V
VREF DELAY GND | +12V | +12V +12V | GND

## GND A. 12 V AUXILIARY SUPPLY

GND of this board ties to the PSU GND star at ONE point (J309). Relay coil current never flows through the amplifier signal ground (docs/13). D306-D309 = full bridge: AC_A/AC_B -> D306/D307 cathodes = RAW; D308/D309 anodes = GND. RAW ~15-17 VDC at ~120 mA (3 x 33 mA G2RL coils + logic). 7812 dissipates ~0.6 W: clip heatsink or bolt to chassis. Ripple 2200u @120 mA ~0.5 Vpp (docs/14 6.5).

## B. UPC1237 PROTECTOR (UTC QW-R107-065.B)

Thresholds: pin 2 +0.62 V / -0.17 V (DC), pin 4 0.74 V (AC-off), pin 8 = 3.4 V reference, pin 6 sinks <= 80 mA.

Flyback diode for K_BYP sits on the MAINS board next to the coil (D403). K_TRIG is on the MAINS board, powered by the Z10 trigger, not by this board. NOT DRAWN YET: single-rail-loss detector (docs/13 P5, optional), over-temperature (P6, optional). Component values are first-pass; every timing and threshold is to be measured per docs/14 9 before the board goes into the chassis.

Pin 1 (overload) and pin 3 grounded: overload detector unused, automatic reset. For LATCH put 22n from pin 3 to GND instead. DC trip (one channel, other at 0 V): +1.24 V / -0.34 V at the speaker output. 56k||56k x 100u = 2.8 s: 30 V fault trips in ~120 ms; 25 Vpk at 10 Hz leaves 0.07 V at pin 2 (<0.17 V). AC-off: 17 Vpk x 10k/66k = 2.6 V at pin 4 while mains is on (droop between peaks to 1.8 V); after loss 10k x 4.7u decays below 0.74 V in ~60 ms (docs/14 6.4 budget <60 ms).

D. SOFT-START BYPASS TIMER: K_BYP (on MAINS board) pulls in ~1.1 s after +12V (docs/14 6.2 recommends 1 s)
E. FRONT PANEL LEDS: green = speakers ON (from RLY), red = +12V present but relay OFF (returns into RLY) Red LED returns into RLY: lit while RLY sits low (~6 mA through the coils, far below pull-in), dark once Q301 pulls RLY high. t = 220k x 22u x ln(12/9.5) = 1.1 s. TL431 snaps at 2.5 V (sharp, no relay chatter); R315 adds ~0.3 V hysteresis; D305 empties C308 within ms at power-off so a quick off-on restarts the NTC limit.

CTRL BOARD V0.6 / FIRST CIRCUIT DRAFT 2026-10-01 / UPC1237 protector + 12 V aux + soft-start timer / NO HARDWARE MEASUREMENT

Opto collector -> amplifier RUN (R8 end), emitter -> that board VEE: closes the JP1 position, 1.3 mA. Two independent paths; the L and R mute nodes stay isolated (docs/13).

Supply: T1 12 VAC winding (12.27 V no-load measured 2026-10-01, 1 A label) -> bridge -> 2200u -> 7812 -> +12V for relays, logic and UPC1237.

Opto must stand |VEE| = 36 V when off: SFH617A-3 (70 V, DIP-4) or H11D1 (300 V, DIP-6); NOT PC817 (35 V). LED chain 2 x 1.2 V at ~8 mA from RLY through R309. Speaker return wire goes straight from the binding post to the amplifier J2.2 / J4.2, never through this board (docs/14 4).

Relay DC breaking: G2RL-1-E is rated 30 VDC; a 33.5 V / 8 ohm fault (4.5 A) is a one-shot protective break, accepted 2026-10-01 (docs/14 6.3 asks >=36 VDC).

## C. SPEAKER RELAYS (G2RL-1-E 12VDC, 16 A, 2 x 33 mA), MUTE OPTOS, STATUS LEDS

D306
1N4007

K

1

A 2 D307

1N4007

K

1

A 2 | D308 1N4007
| K

1

A 2 D309

1N4007

K

1

A 2

D305
1N4148 (fast reset) K

1

A 2 R312

220k

1 | 2
