ewinkuo1-sudo/diy-lm3886-amplifier/electrical/preview/mains-v01.pdf

1 | 2 | 3 | 4 | 5 | 6 | 7 | 8
1 | 2 | 3 | 4 | 5 | 6 | 7 | 8

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
## F Date: 2026-10-01

KiCad E.D.A. 10.0.6 | Id: 1/1
Size: A3 | Rev: 0.6 FIRST DRAFT

# Title: LM3886 V0.6 mains soft-start / trigger board (MAINS) - LIVE MAINS

## File: mains-v01.kicad_sch

## Sheet: /

## V0.6 mains board / circuit draft only / LIVE MAINS / no hardware measurements

K

1

A 2 D402

## 1N4007 flyback

A1 A1

A2 A2 | COMCOM

## NO NO K401 K_TRIG G2RL-1-E 12VDC (16 A) 1

1

2

2 J402

## FRONT POWER SWITCH

1

1

2

2 J405

## TO T1 PRIMARY (L, N) K

1

A 2 D401

## 1N4007 series (reverse-polarity) 1

1

2

2 J401
FROM IEC + FUSE (L, N) | K

1

A 2 D403

## 1N4007 flyback

1 | 2 RT401

## SL22 10005 (10R / 5A / 90J) A1 A1

A2 A2 | COMCOM

## NO NO K402 K_BYP G2RL-1-E 12VDC (16 A) 1

1

2

2 J404

## FROM CTRL J306 (BYP_HI, GND) 1

1

2

2 J403

## Z10 12V TRIGGER (tip +, sleeve -)

L_T1 GND_CTRL

L_SW

BYP_HI TRIG_N | L_SW

L_IN

TRIG_IN

BYP_HI | L_SW
L_T1 GND_CTRL | N_IN
BYP_HI | GND_CTRL

L_IN

TRIG_P N_IN

TRIG_P

L_IN

L_SW

TRIG_N

TRIG_IN

L_T1

TRIG_P | TRIG_N K_TRIG coil 33 mA at 12 V from the Z10 trigger output (<= 50 mA budget, Z10 spec unknown). Contact in parallel with the front switch (OR). If the Z10 cannot source 33 mA: latch via the 12 V aux (docs/14 6.7). NTC: primary 1.79 A rms steady (197 VA label), 10 ohm cold limits the first half-cycle to ~15 A; 90 J rating vs 38 J estimated absorption (docs/14 6.2). Bypassed after ~1.1 s by K402.

If K402 never pulls in, RT401 carries 1.79 A continuously: SL22 10005 is rated 5 A steady, so it survives (hot, ~1 ohm) - the failure is only lost inrush limiting on a quick off-on. Mains-side parts: J401, J402, J405, RT401, K401/K402 contacts. Low-voltage: K401/K402 coils, D401-D403, J403, J404. Keep >= 6.4 mm creepage; slot under the relays.

MAINS BOARD V0.6 / FIRST CIRCUIT DRAFT 2026-10-01 / LIVE 110 VAC: creepage >= 6.4 mm between mains and the 12 V coil side, PE to chassis stud (not on this board)

Path (docs/14 2): IEC inlet + fuse holder (chassis) -> J401 -> [manual switch J402 || K_TRIG contact] -> NTC RT401 (K_BYP contact across it) -> J405 -> T1 primary.
