ewinkuo1-sudo/diy-lm3886-amplifier/electrical/preview/internal-psu-v02.pdf

1 | 2 | 3 | 4 | 5 | 6 | 7 | 8
1 | 2 | 3 | 4 | 5 | 6 | 7 | 8

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
Size: A3 | Rev: 0.3 DRAFT | F Date: 2026-09-22
KiCad E.D.A. 10.0.6 | Id: 1/1

## Title: LM3886 internal PSU - isolated secondaries only

File: internal-psu-v02.kicad_sch

Sheet: /

Internal PSU system / PCB V0.3 engineering draft only / no hardware measurements

# 1 2 C208 TBD Cs (150n / 630V film) 1 2 C209 TBD Cx (10n / 630V film)

~1 AC1

~2 AC2 | -

N +

P BR2 >=15A / >=200V TBD

~1 AC1

~2 AC2 | -

N +

P BR1 >=15A / >=200V TBD

1 2 R203 TBD Rs (10R-47R / 2W) 1 2 C207 TBD Cx (10n / 630V film)

1 | 2 R201
2.2k / 2W BLEED
1 | 2 F201
TBD per transformer

# 1 2 C210 TBD Cs (150n / 630V film) 1

1

2

2 J201
T1 SEC 1

1

1

2

2 J202
T1 SEC 2
1 | 2 C201
10000u / 63V
1 | 2 F202
TBD per transformer 1 2 | R204 | TBD Rs (10R-47R / 2W)
1 | 2 C203
10000u / 63V
1 | 2 C204
10000u / 63V

1

1

2

2

3

3 J204
TO R AMP J5
1 | 2 R202
2.2k / 2W BLEED
1 | 2 C206
100n / 100V film
1 | 2 C202
10000u / 63V
1 | 2 C205
100n / 100V film

1

1

2

2

3

3 J203
TO L AMP J5

NEG_AC1

POS_SNUB

POS_AC2 NEG_SNUB NEG_AC1

POS_AC_FUSED

POS_AC2 | GND NEG_AC2 | NEG_AC2 NEG_AC_FUSED

GND

NEG_AC2

VCC

VCC

NEG_AC2

GND

GND

VCC

VEE | GND | VEE
POS_AC2 | GND | VEE

POS_AC1

GND | VEE NEG_AC1

POS_AC1

GND | VEE

POS_AC2

VCC | GND NEG_AC1
VCC | GND
POS_AC1 | GND

VCC

POS_AC1

VEE

VCC

VEE GND

## INTERNAL LINEAR PSU / V0.3 / PLAN C / SECONDARY-SIDE DRAFT

T1 ordered: 110 VAC primary; 2 x 22 VAC independent + 12 VAC auxiliary. Seller: 200 W; VA / currents TBD.

C201/C202: positive lead to VCC. C203/C204: positive lead to GND.

C plan: 20,000 uF per rail. C201-C204 CDE 381LX delivered 2026-09-23 (D35 x 50, snap-in). BR1/BR2 KBPC2510 bolt to chassis, 4 Faston wires each to a board terminal; NOT purchased. Fuse ratings / bridge cooling / inrush / PE chassis bond / speaker protection: design and verify before assembly. 12 VAC auxiliary: reserved for control / speaker protection; AC vs DC module input and current rating TBD. Separate schematic projects: J203 (L) and J204 (R) pin 1/2/3 each wire to one amplifier J5 pin 1/2/3 as a twisted triple. Same-label text does not wire the two files. V0.4: R203/C207/C208 and R204/C209/C210 are snubber PROVISIONS (footprints only). Fit only after measuring secondary ringing with the actual transformer and bridge.

V0.4 SNUBBER PROVISION across winding: Cx || (Rs + Cs). Values TBD by ringing test; not fitted at first power-up. NEG RAIL / floating 22 VAC secondary

POS RAIL / floating 22 VAC secondary

V0.4 SNUBBER PROVISION across winding: Cx || (Rs + Cs). Values TBD by ringing test; not fitted at first power-up.

Two bridges; connect BR1 negative to BR2 positive at the reservoir star point. Do not pre-join the AC windings. R203 | TBD Rs (10R-47R / 2W) 1 2 C207 | TBD Cx (10n / 630V film) 1 2 | F201
TBD per transformer 1 | 2 C208 | TBD Cs (150n / 630V film) 1 2 | F202
TBD per transformer 1 | 2 C209 | TBD Cx (10n / 630V film) 1 2 | R204 | TBD Rs (10R-47R / 2W) 1 2 | C210 | TBD Cs (150n / 630V film) 1 2
