ewinkuo1-sudo/diy-lm3886-amplifier/docs/diagrams/lm3886_complete.png

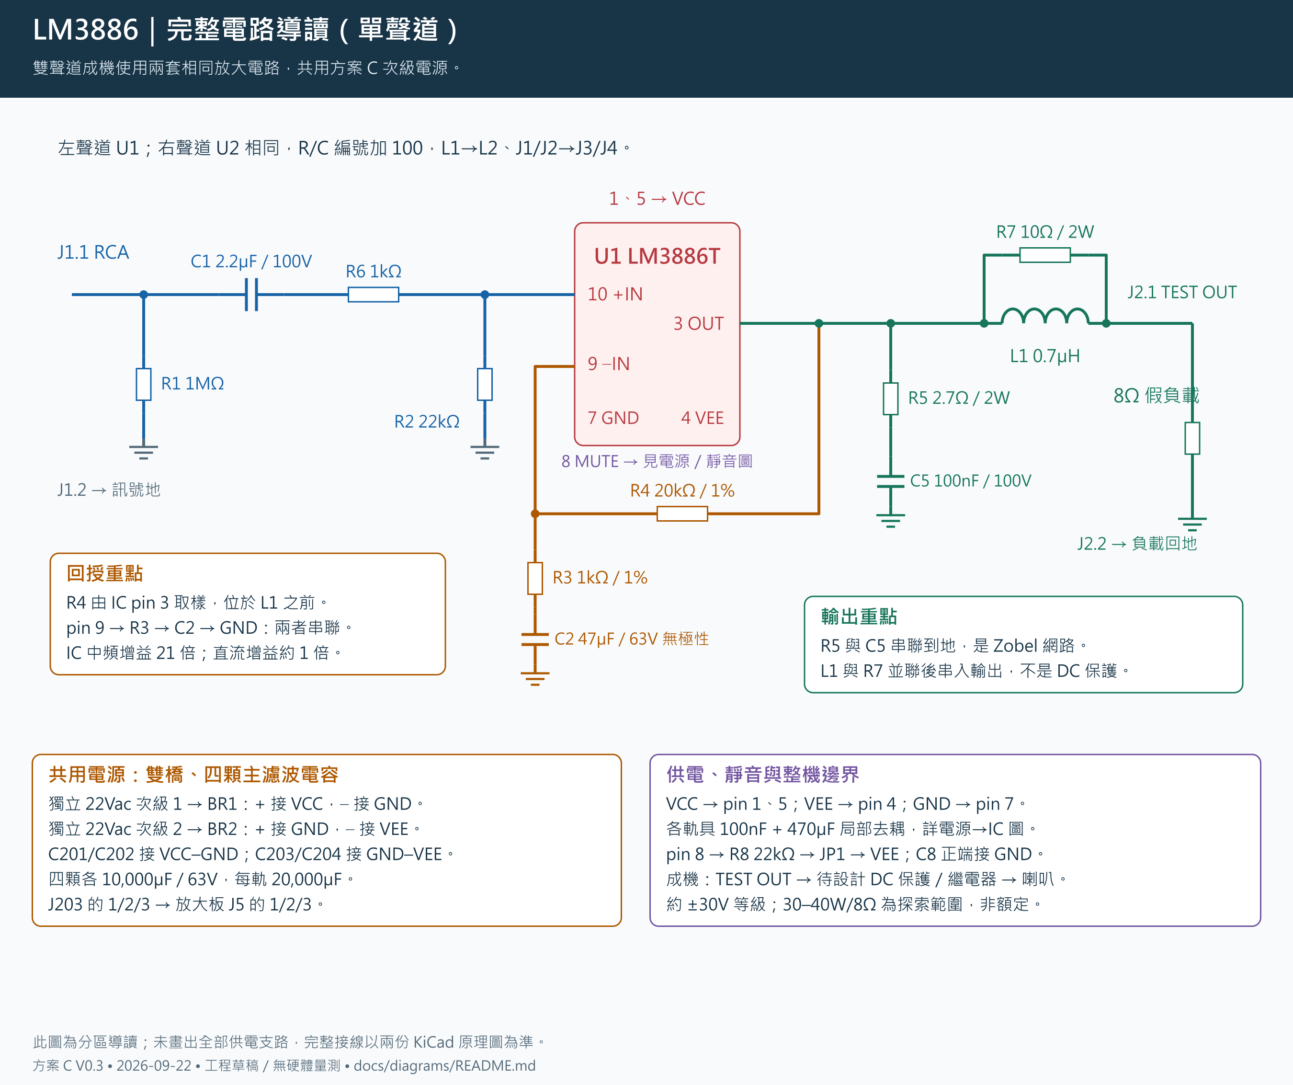
docs/diagrams/lm3886_complete.png
