ewinkuo1-sudo/diy-lm3886-amplifier/docs/diagrams/lm3886_ic_to_output.png

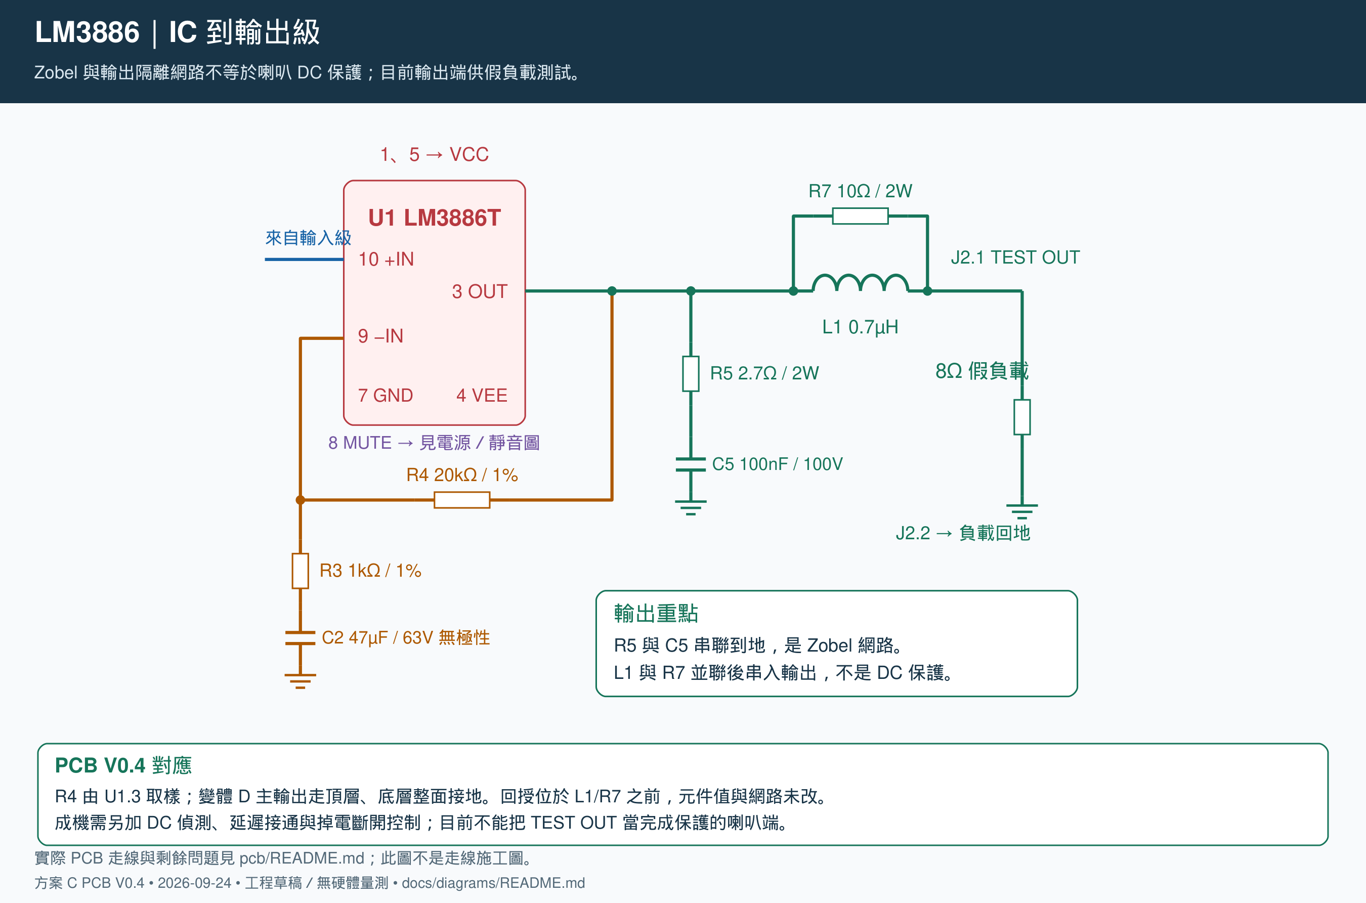
docs/diagrams/lm3886_ic_to_output.png
