ewinkuo1-sudo/diy-lm3886-amplifier/docs/diagrams/lm3886_psu_sch_annotated.png

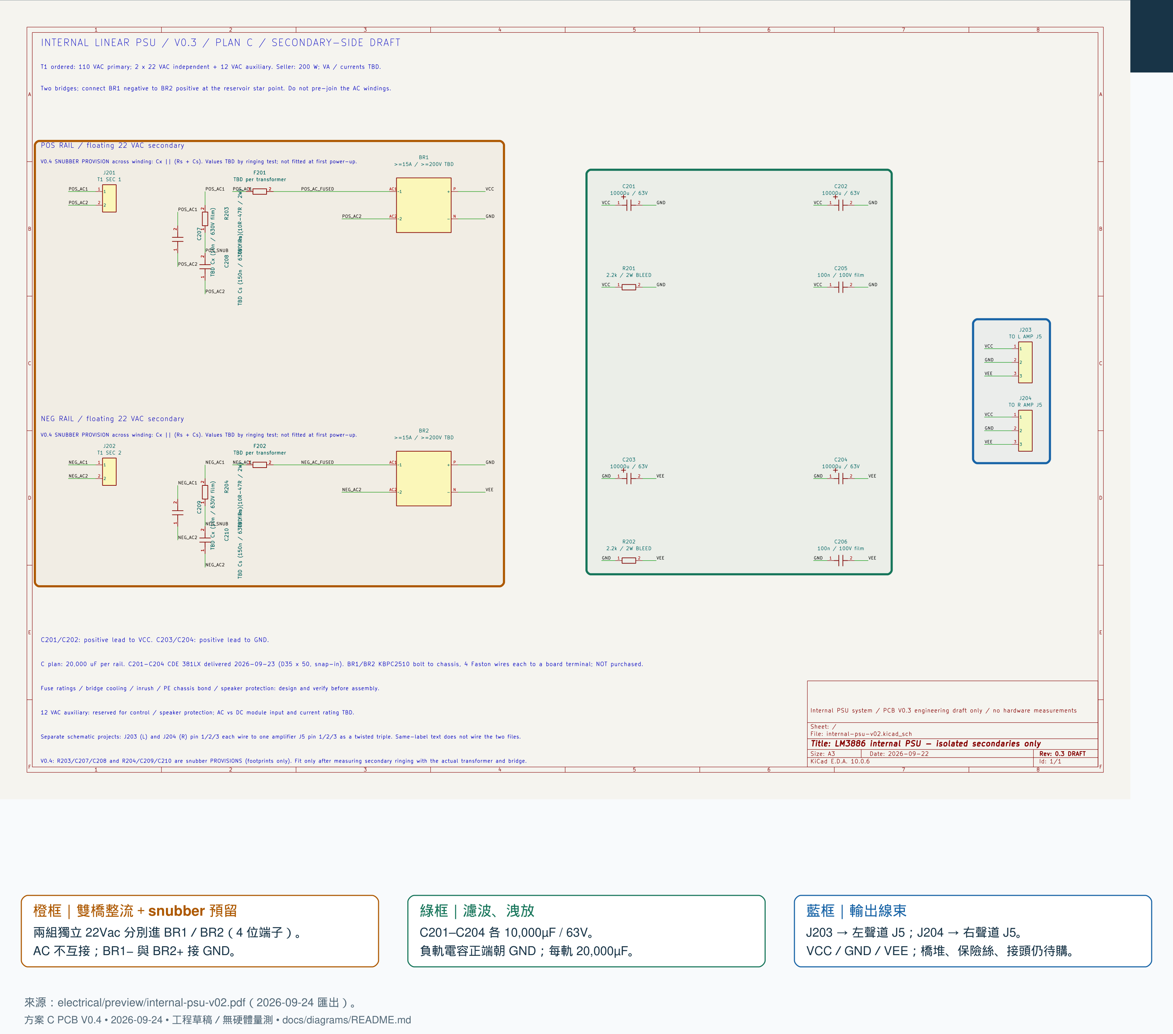
docs/diagrams/lm3886_psu_sch_annotated.png
