ewinkuo1-sudo/diy-lm3886-amplifier/docs/photos/20260923-transformer-arrival.jpg

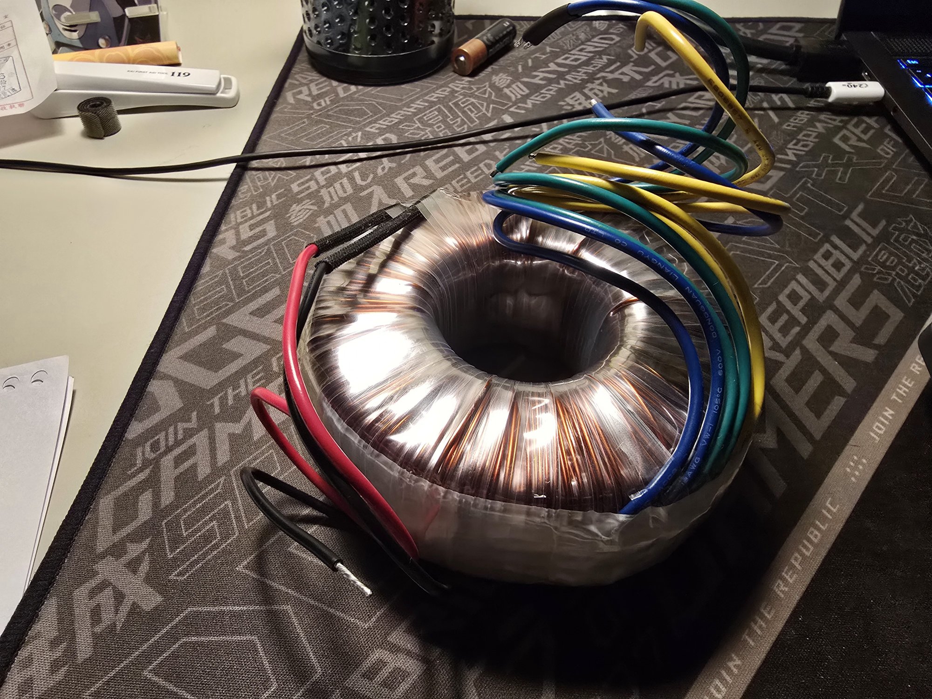
docs/photos/20260923-transformer-arrival.jpg
