ewinkuo1-sudo/diy-lm3886-amplifier/docs/photos/20260929-lm3886t-arrival.jpg

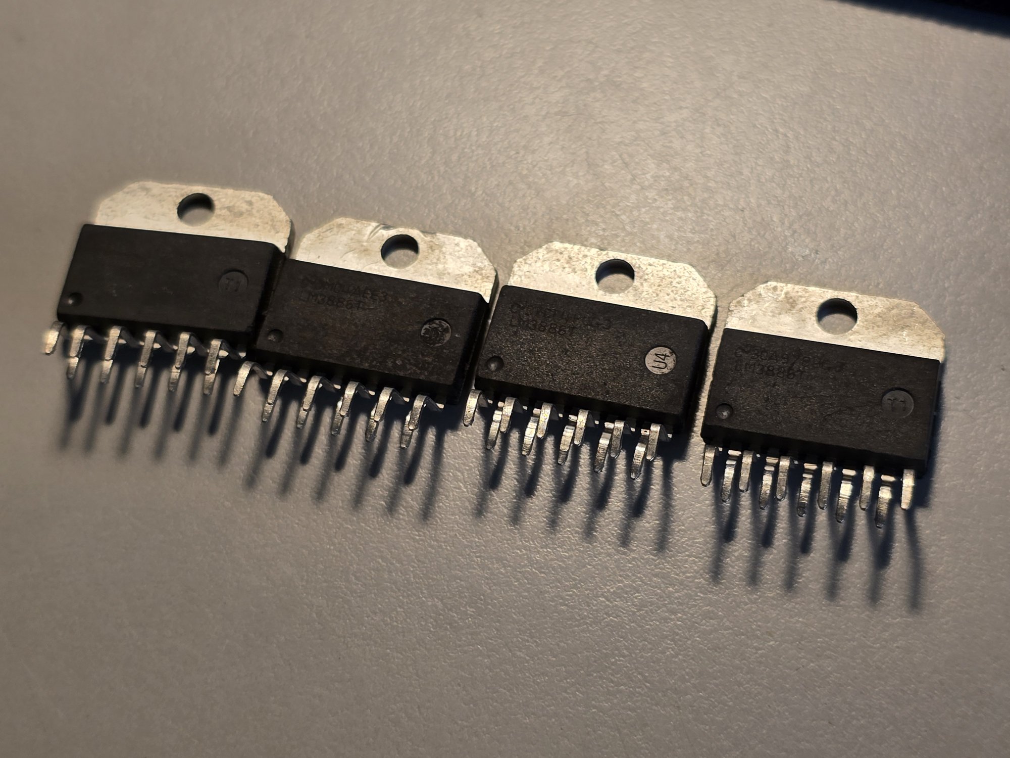
docs/photos/20260929-lm3886t-arrival.jpg
