ewinkuo1-sudo/diy-lm3886-amplifier/docs/photos/20261001-transformer-electrical.jpg

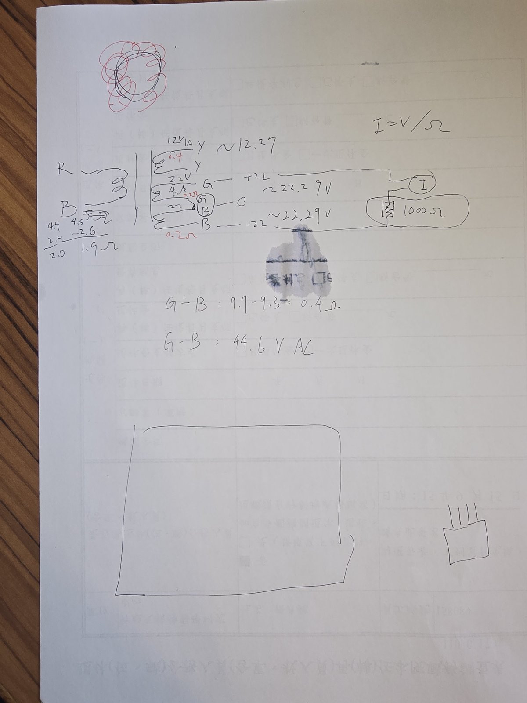
docs/photos/20261001-transformer-electrical.jpg
