ewinkuo1-sudo/diy-lm3886-amplifier/pcb/inspection-v051/3d/mono-isometric.png

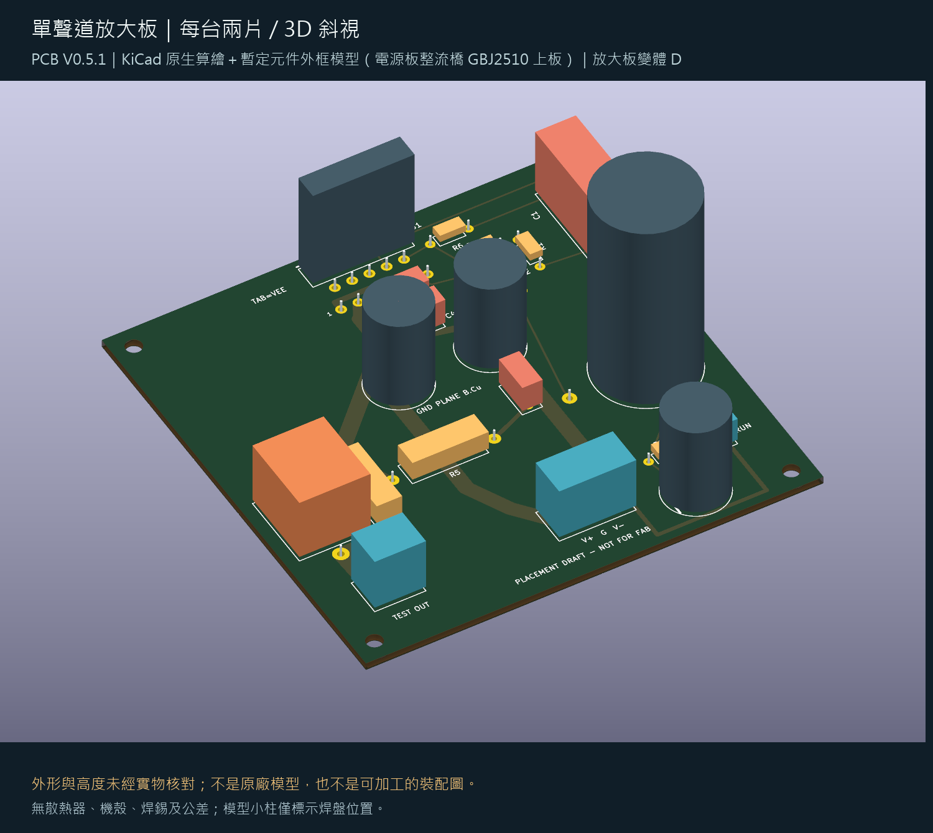
pcb/inspection-v051/3d/mono-isometric.png
