ewinkuo1-sudo/diy-lm3886-amplifier/pcb/inspection-v051/3d/psu-top.png

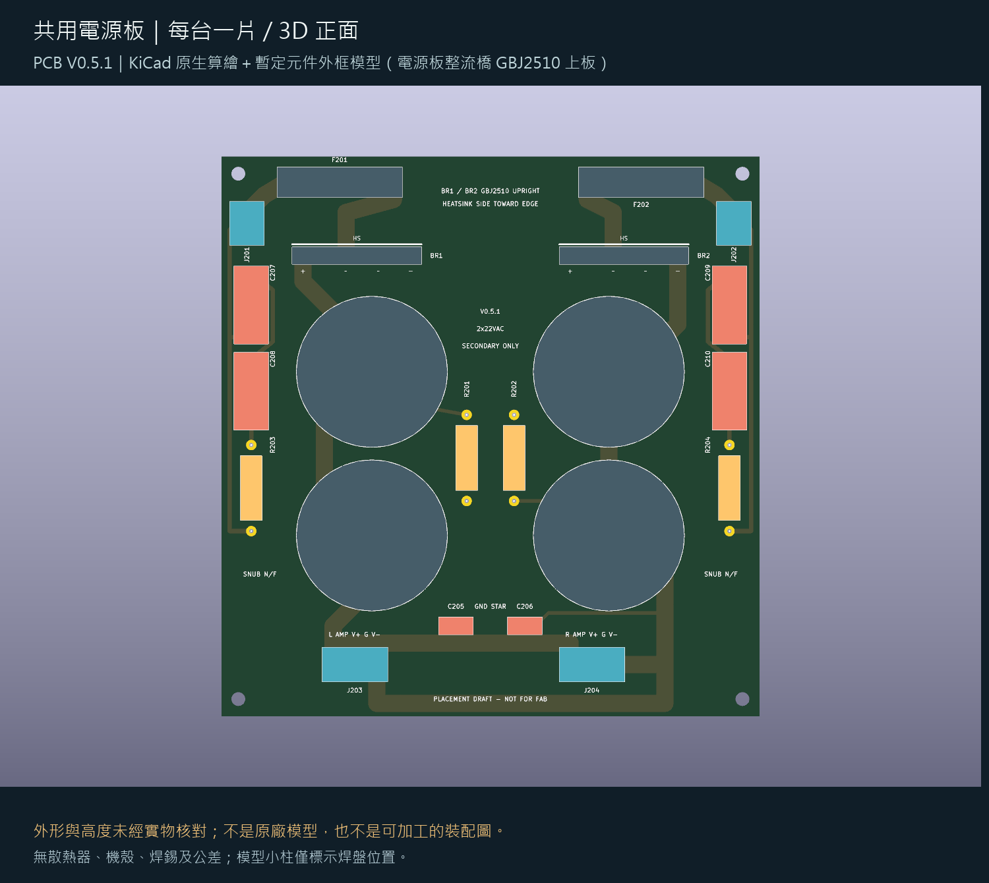
pcb/inspection-v051/3d/psu-top.png
