ewinkuo1-sudo/diy-lm3886-amplifier/pcb/inspection-v051/drawings/mono-top.png

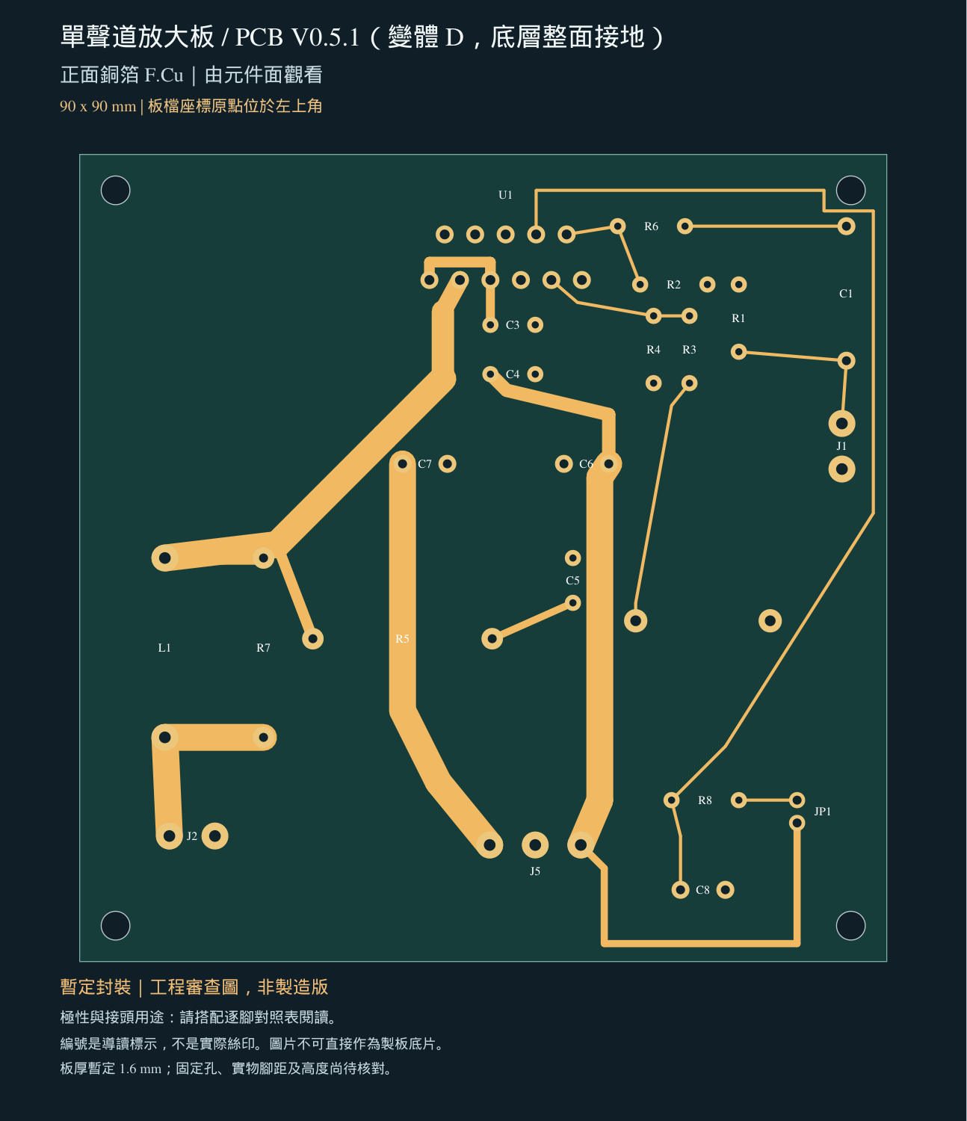
pcb/inspection-v051/drawings/mono-top.png
