ewinkuo1-sudo/diy-lm3886-amplifier/pcb/preview/mono-layout-v03.png

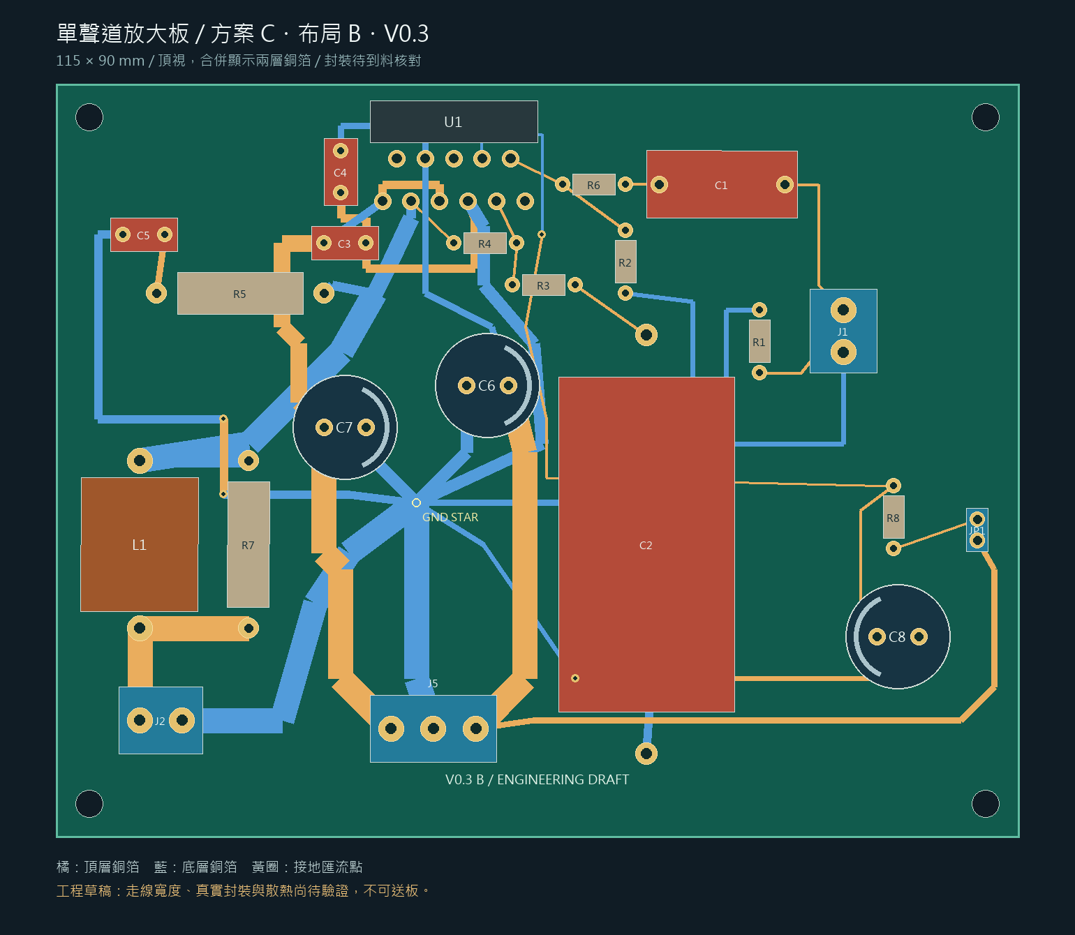
pcb/preview/mono-layout-v03.png
