ewinkuo1-sudo/diy-lm3886-amplifier/pcb/preview/mono-layout-v05d.png

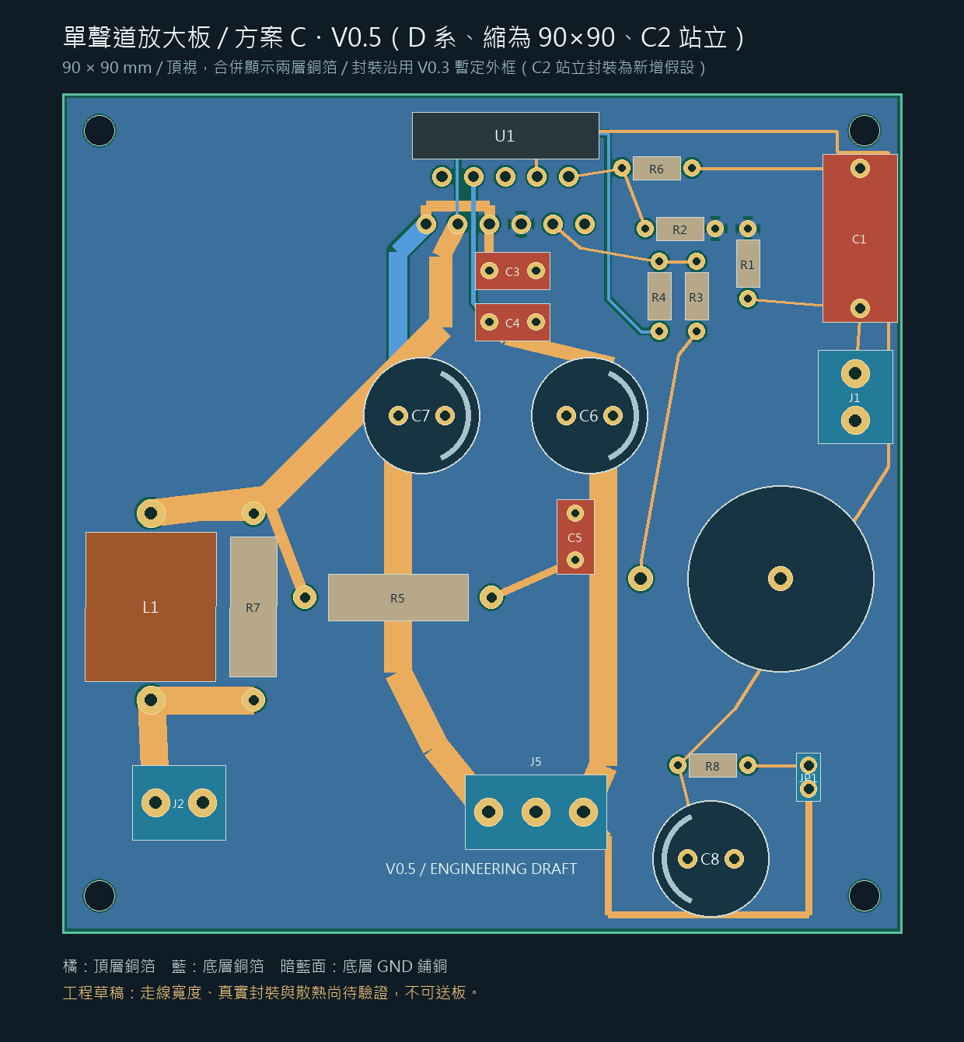
pcb/preview/mono-layout-v05d.png
