ewinkuo1-sudo/diy-lm3886-amplifier/pcb/preview/mono-placement-v01.png

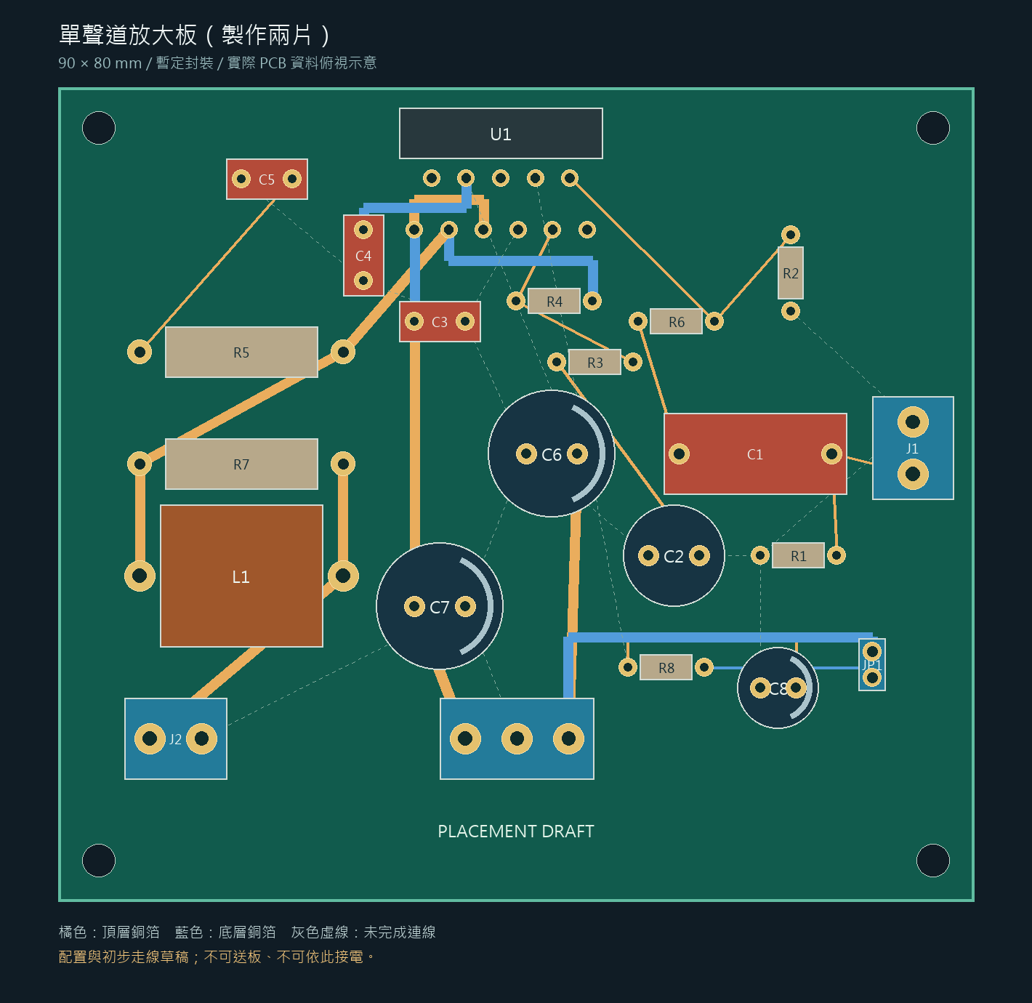
pcb/preview/mono-placement-v01.png
