ewinkuo1-sudo/diy-lm3886-amplifier/pcb/preview/psu-layout-v02.png

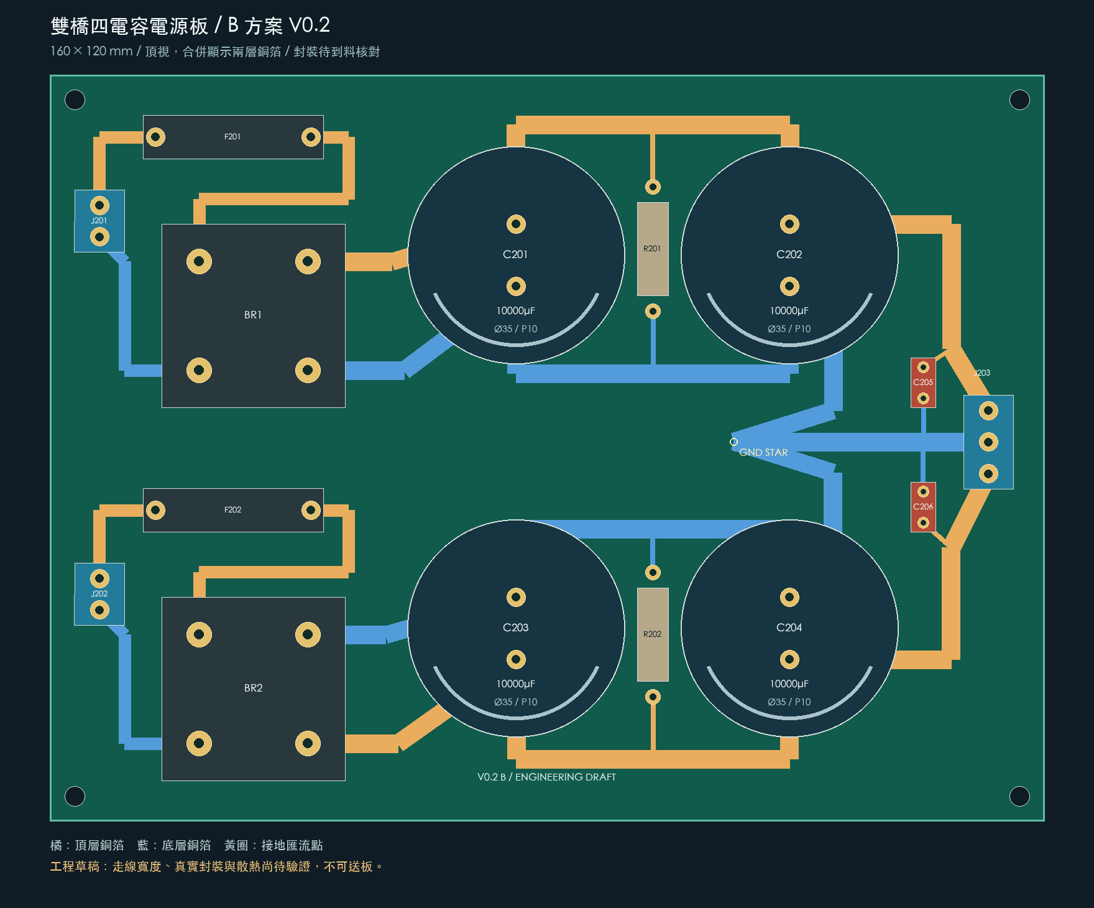
pcb/preview/psu-layout-v02.png
