ewinkuo1-sudo/diy-lm3886-amplifier/pcb/preview/psu-placement-v01.png

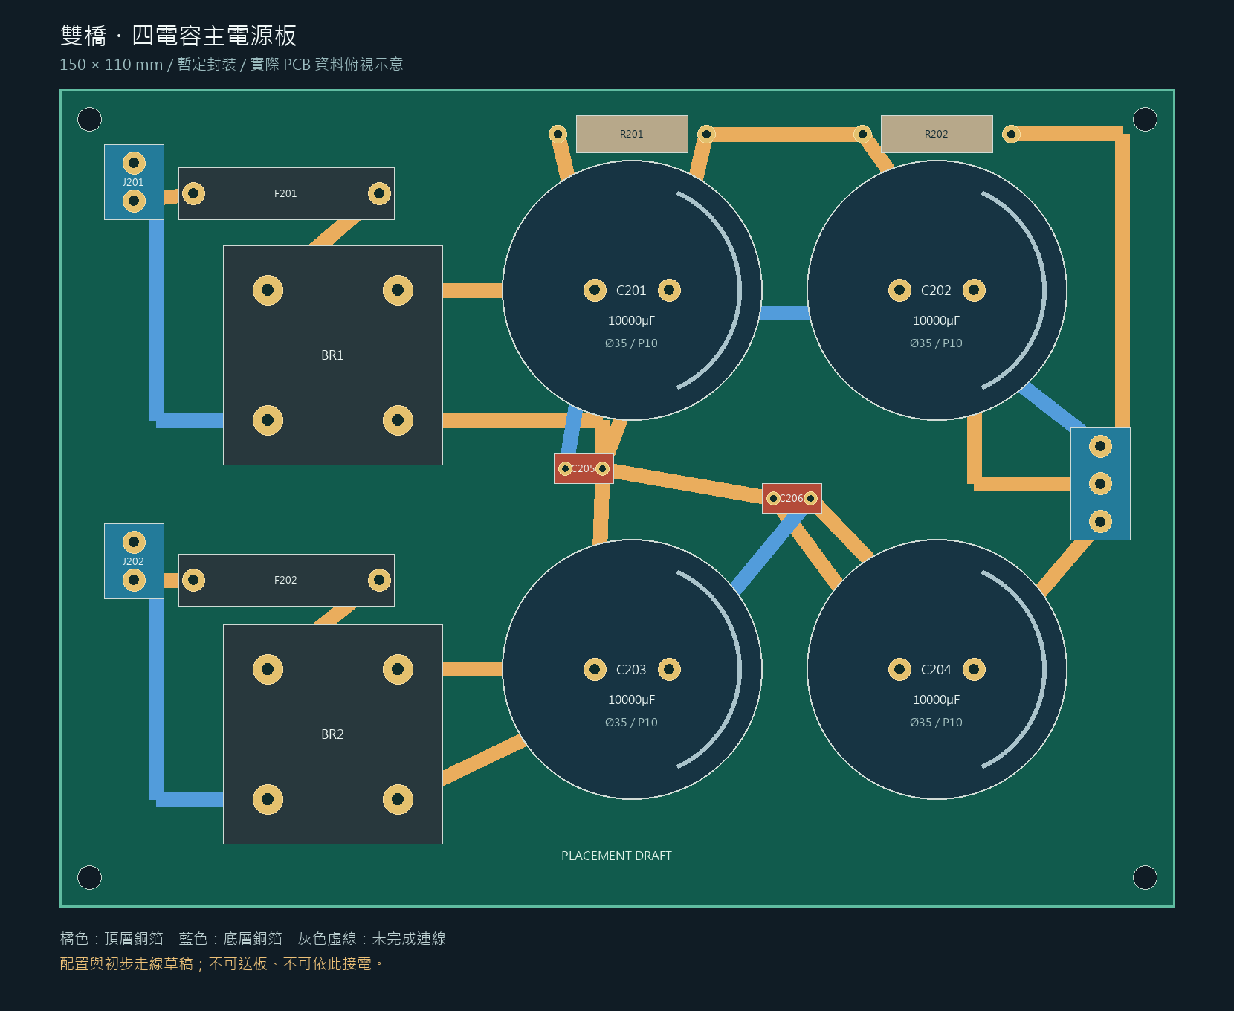
pcb/preview/psu-placement-v01.png
