ewinkuo1-sudo/diy-lm3886-amplifier/pcb/preview/system-layout-v04.png

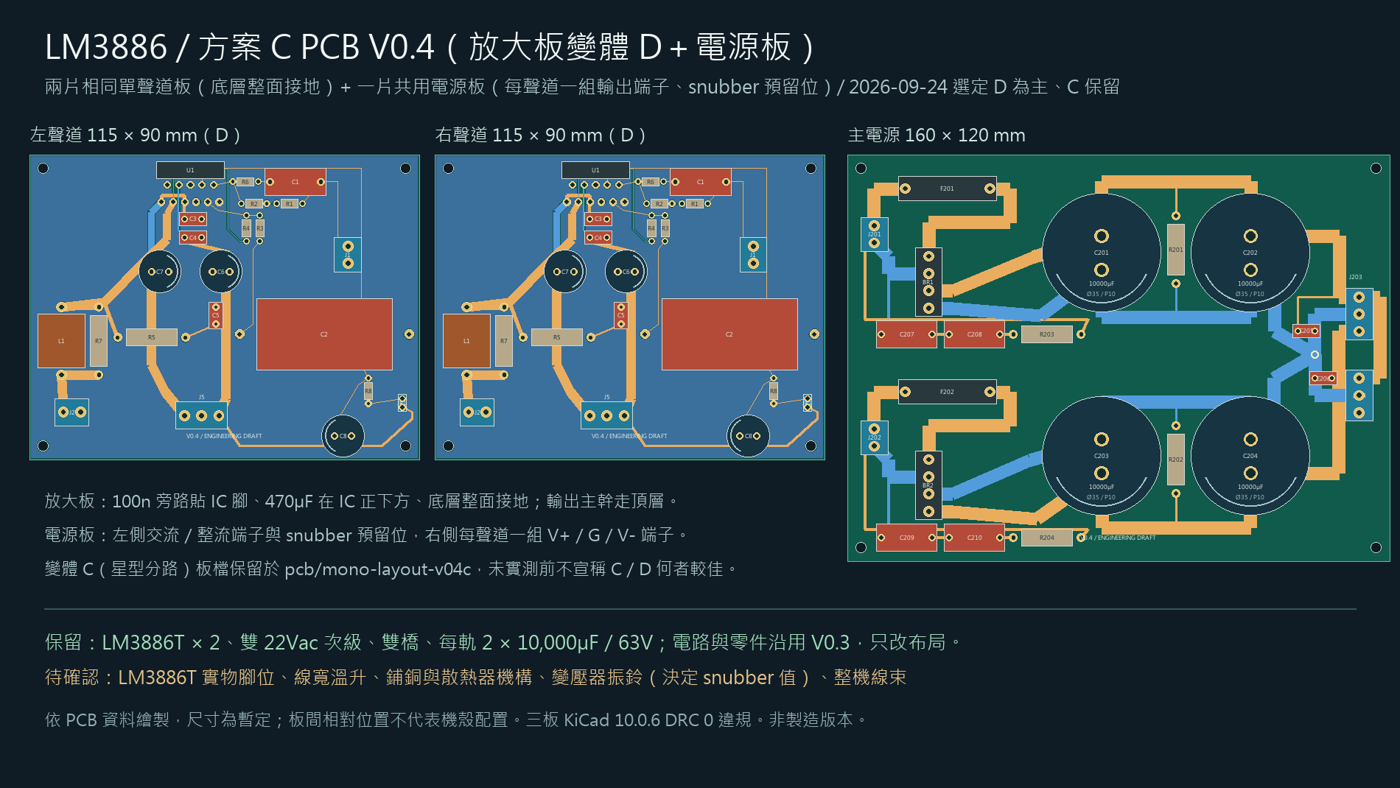
pcb/preview/system-layout-v04.png
