ewinkuo1-sudo/diy-lm3886-amplifier/pcb/preview/system-layout-v051.png

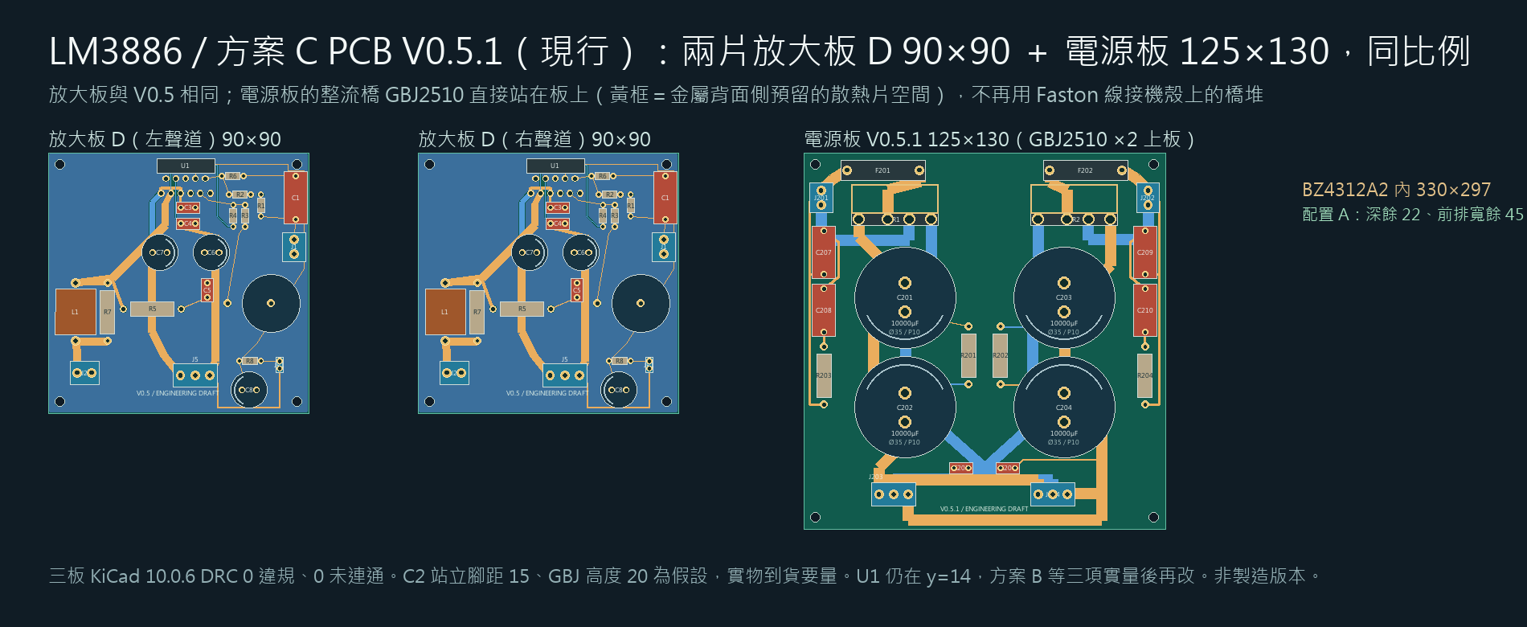
pcb/preview/system-layout-v051.png
