ewinkuo1-sudo/diy-lm3886-amplifier/docs/photos/20260922-parts-arrival.jpg

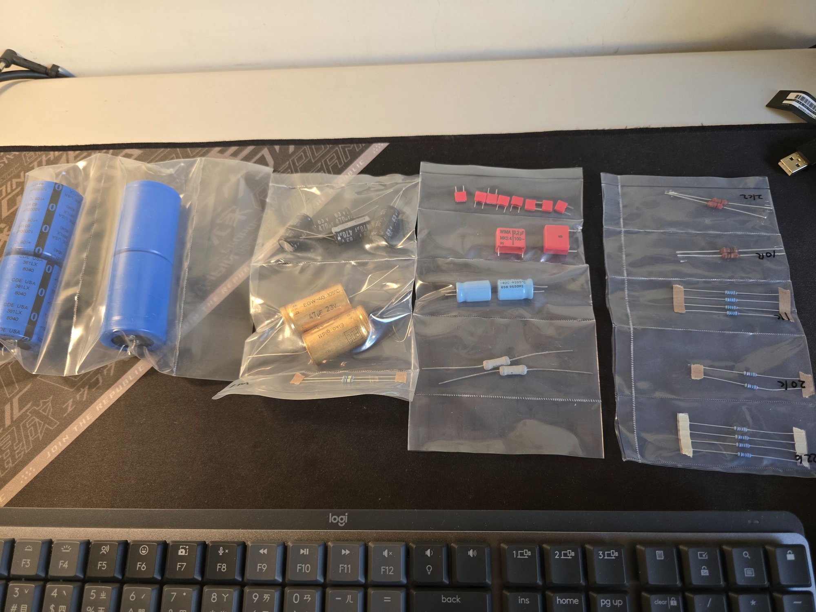
docs/photos/20260922-parts-arrival.jpg
